mklangkamp/BeachbotsMatt/Basebot Stand/ZEDCamera.SLDPRT

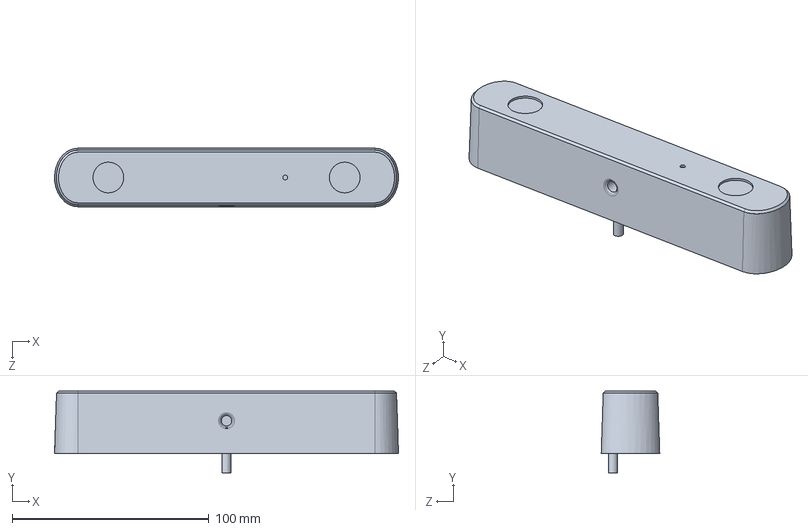
[picture p15: CAD file, 2021-02-08]
Basebot Stand/ZEDCamera.SLDPRT
174.7 x 41.6 x 29.7 mm
