mklangkamp/BeachbotsMatt/Basebot/Steering Motor Mount (Bottom).SLDPRT

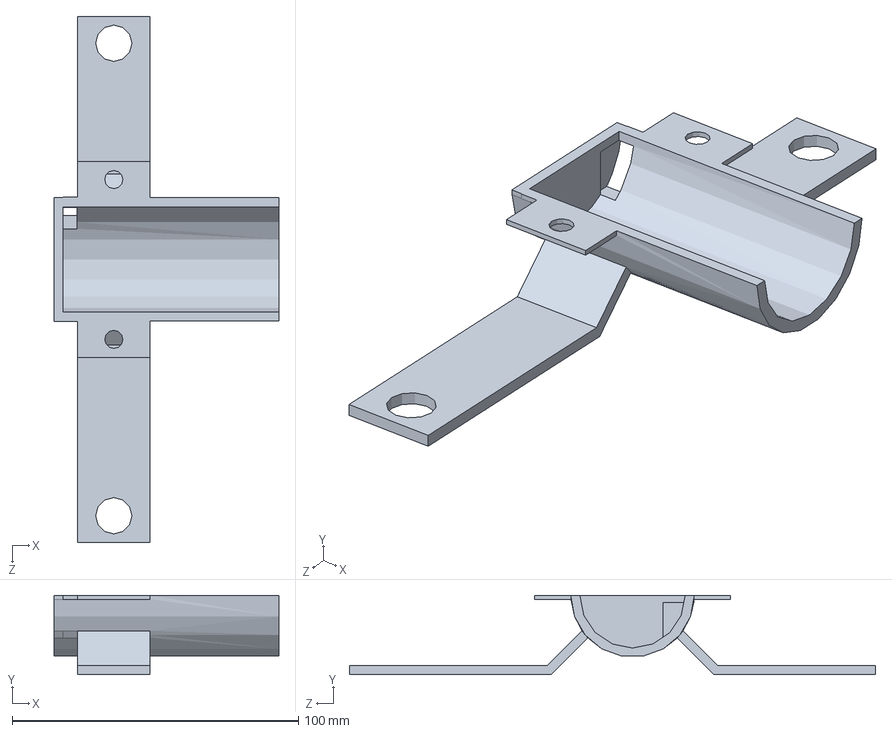
[picture p16: CAD file, 2021-05-04]
Basebot/Steering Motor Mount (Bottom).SLDPRT
78.6 x 27.7 x 183.8 mm
