mklangkamp/BeachbotsMatt/Chassis/CAM (Esprit)/SuspensionPlateAfter1.STL

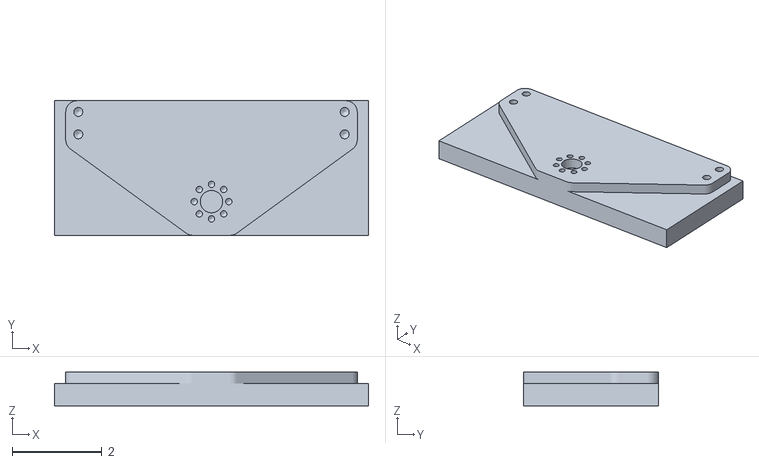
[picture p17: CAD file, 2020-11-09]
Chassis/CAM (Esprit)/SuspensionPlateAfter1.STL
7.00 x 3.00 x 0.75
