mklangkamp/BeachbotsMatt/Chassis/Electronics mount/raspberry pi 4b mount.SLDPRT

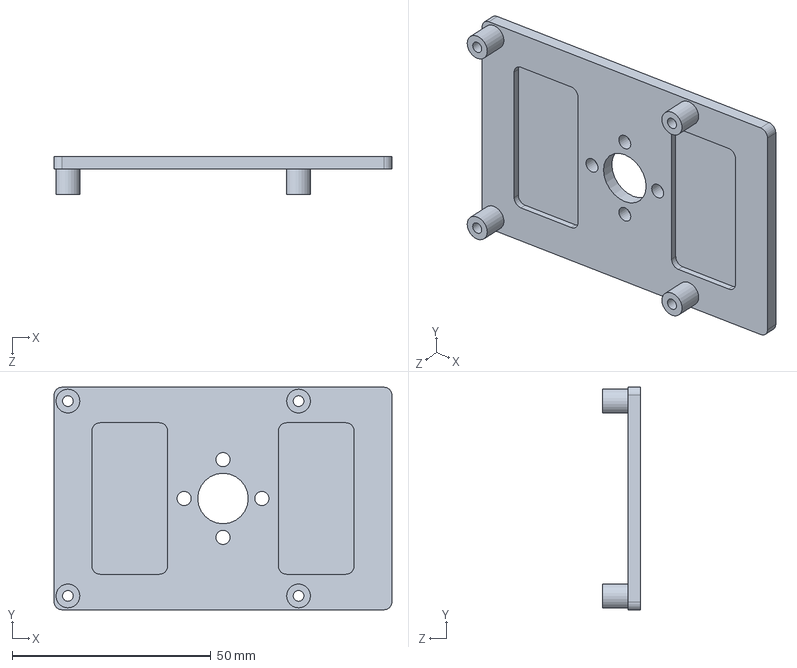
[picture p18: CAD file, 2020-11-25]
Chassis/Electronics mount/raspberry pi 4b mount.SLDPRT
85.0 x 56.0 x 9.53 mm
