mklangkamp/BeachbotsMatt/Chassis/GripperAssemblySlot/ServoHornWithSlotAttachment.SLDPRT

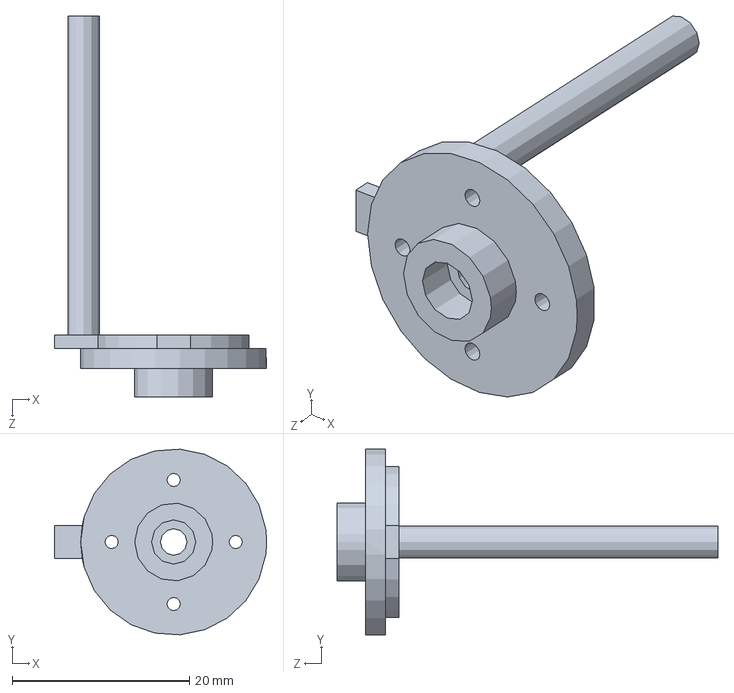
[picture p19: CAD file, 2021-05-04]
Chassis/GripperAssemblySlot/ServoHornWithSlotAttachment.SLDPRT
24.0 x 21.0 x 43.0 mm
