mklangkamp/BeachbotsMatt/Chassis/GrippperAssemblyNEW/Involute Spur Gear Generator - Better 0 3-13 WIDER.SLDPRT

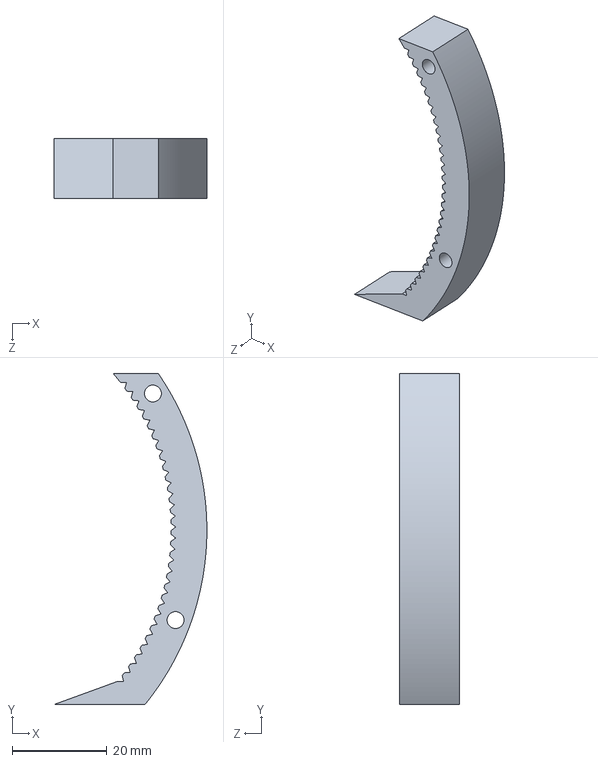
[picture p20: CAD file, 2021-03-24]
Chassis/GrippperAssemblyNEW/Involute Spur Gear Generator - Better 0 3-13 WIDER.SLDPRT
32.2 x 69.8 x 12.7 mm
