mklangkamp/BeachbotsMatt/Chassis/LBracketReinforcement.SLDPRT

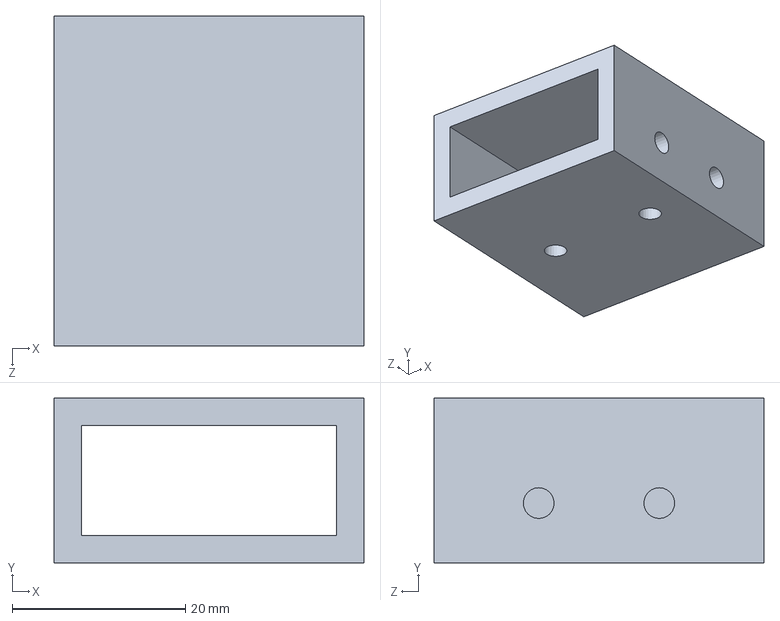
[picture p21: CAD file, 2021-05-04]
Chassis/LBracketReinforcement.SLDPRT
35.8 x 19.1 x 38.1 mm
