mklangkamp/BeachbotsMatt/Basebot Stand/StandOuterShaft.SLDPRT

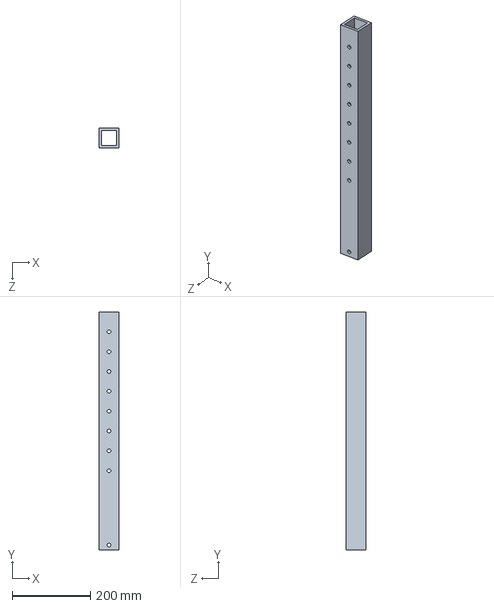
[picture p23: CAD file, 2021-02-08]
Basebot Stand/StandOuterShaft.SLDPRT
50.8 x 609.6 x 50.8 mm
