mklangkamp/BeachbotsMatt/Basebot/Wheel to Axle Adapter.SLDPRT

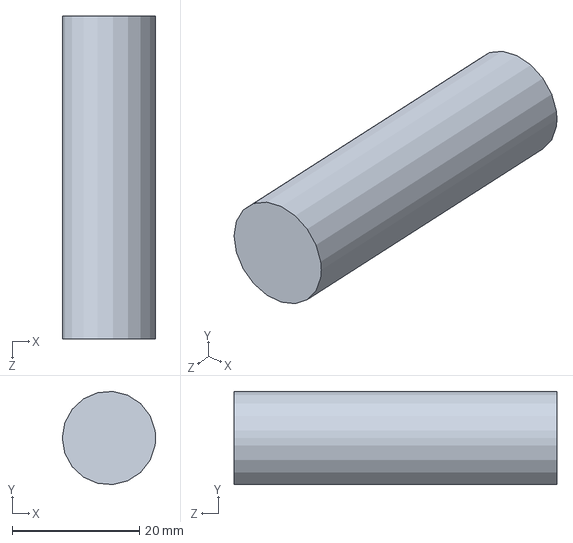
[picture p24: CAD file, 2021-05-04]
Basebot/Wheel to Axle Adapter.SLDPRT
14.7 x 14.6 x 50.8 mm
