mklangkamp/BeachbotsMatt/Chassis/CAM (Esprit)/pillowblockafter2.1.STL

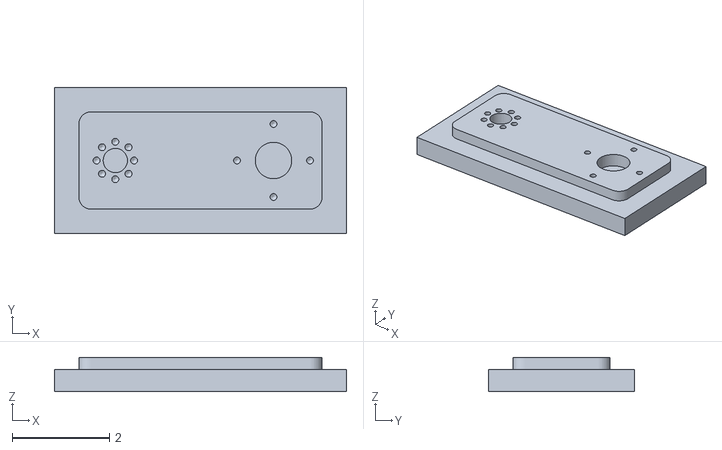
[picture p25: CAD file, 2020-11-09]
Chassis/CAM (Esprit)/pillowblockafter2.1.STL
6.00 x 3.00 x 0.7
