mklangkamp/BeachbotsMatt/Chassis/Electronics mount/stepper motor driver mount.SLDPRT

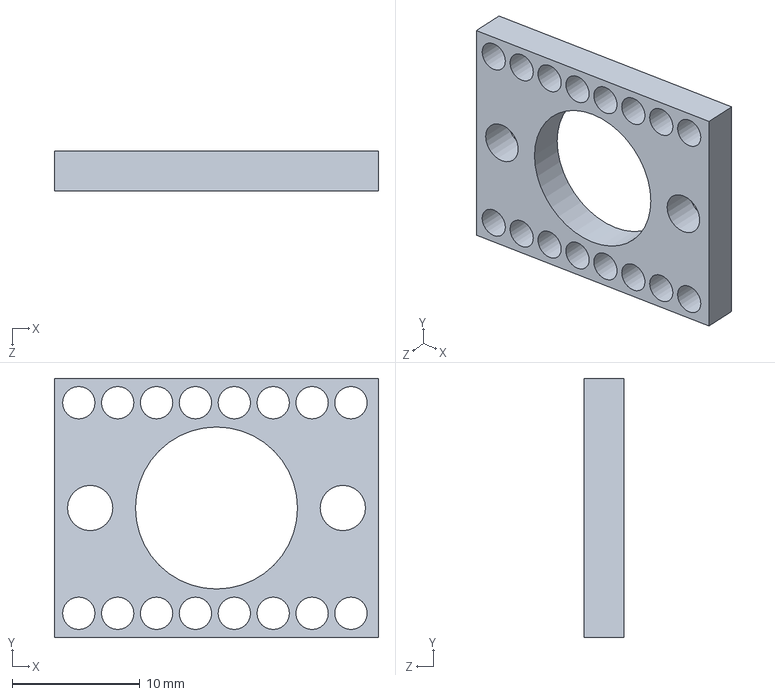
[picture p26: CAD file, 2020-11-23]
Chassis/Electronics mount/stepper motor driver mount.SLDPRT
25.4 x 20.3 x 3.17 mm
