mklangkamp/BeachbotsMatt/Chassis/GripperAssemblySlot/GripperTopBracketNew.SLDPRT

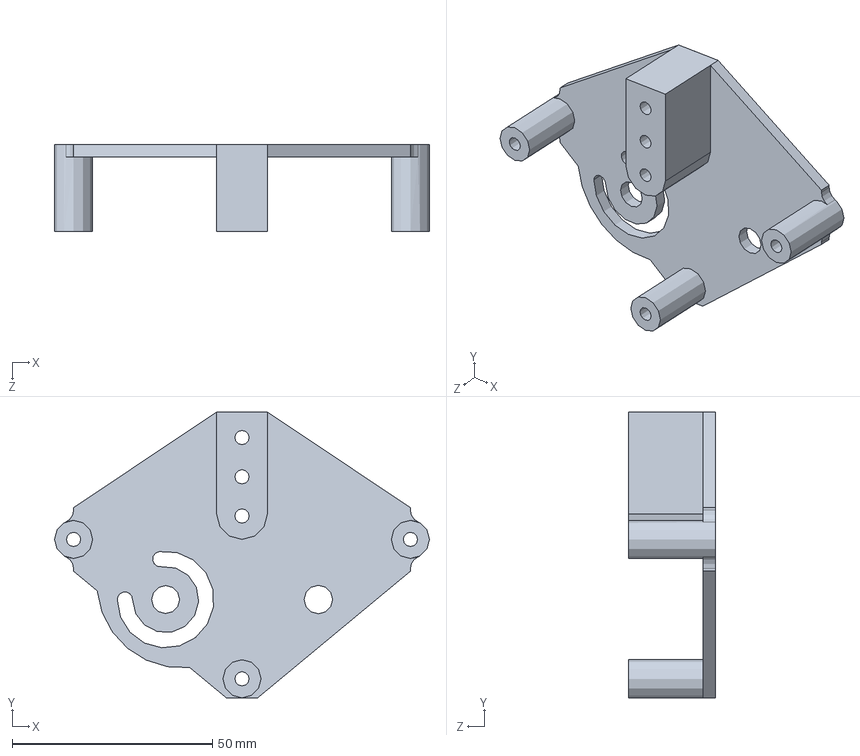
[picture p27: CAD file, 2021-05-04]
Chassis/GripperAssemblySlot/GripperTopBracketNew.SLDPRT
93.5 x 71.3 x 21.7 mm
