mklangkamp/BeachbotsMatt/Chassis/GrippperAssemblyNEW/Involute Spur Gear Generator - Better 0 3-13 EXTRA.SLDPRT

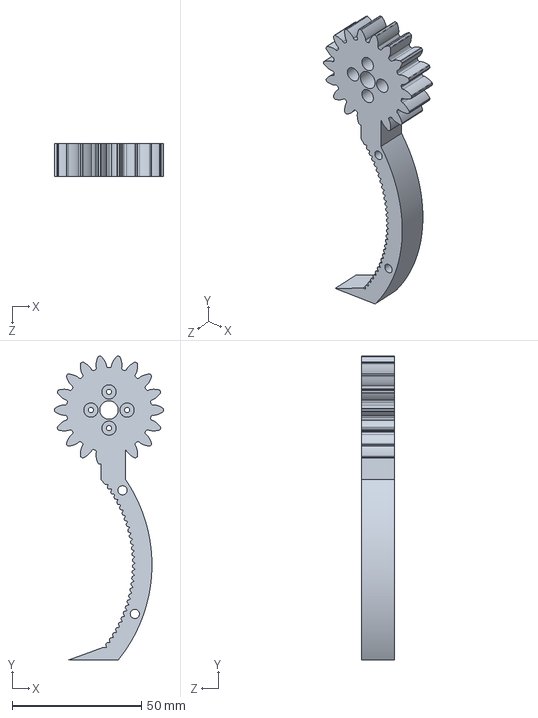
[picture p28: CAD file, 2021-03-24]
Chassis/GrippperAssemblyNEW/Involute Spur Gear Generator - Better 0 3-13 EXTRA.SLDPRT
42.3 x 117.6 x 12.7 mm
