mklangkamp/BeachbotsMatt/Chassis/New Gripper Designs/GripperArmBracket.SLDPRT

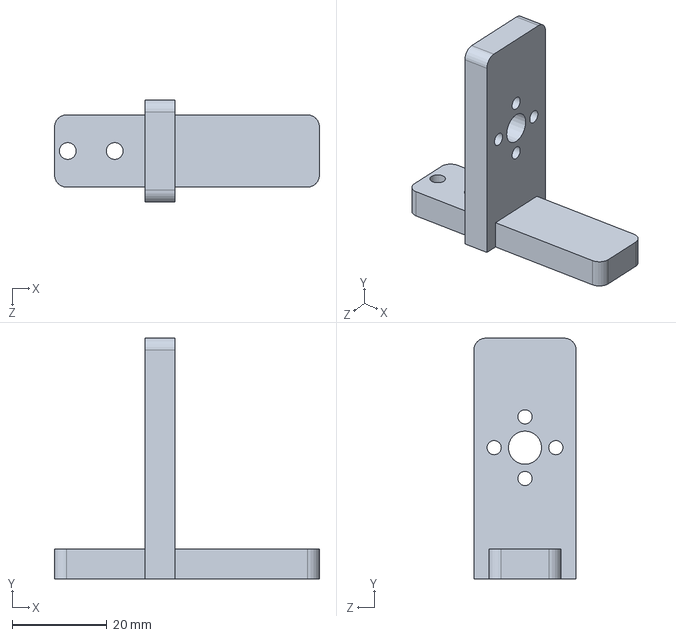
[picture p29: CAD file, 2020-12-01]
Chassis/New Gripper Designs/GripperArmBracket.SLDPRT
55.9 x 50.8 x 21.6 mm
