mklangkamp/BeachbotsMatt/Chassis/New Gripper Designs/GripperRedesignOne/GearBase.SLDPRT

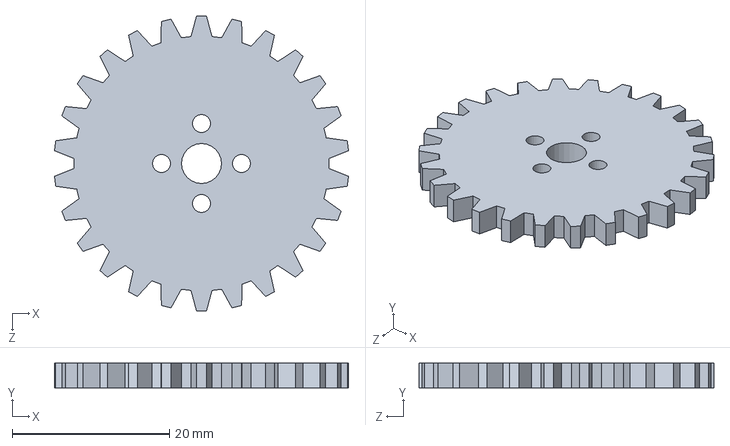
[picture p30: CAD file, 2021-03-08]
Chassis/New Gripper Designs/GripperRedesignOne/GearBase.SLDPRT
37.4 x 3.17 x 37.5 mm
