mklangkamp/BeachbotsMatt/Chassis/power swtich mount.SLDPRT

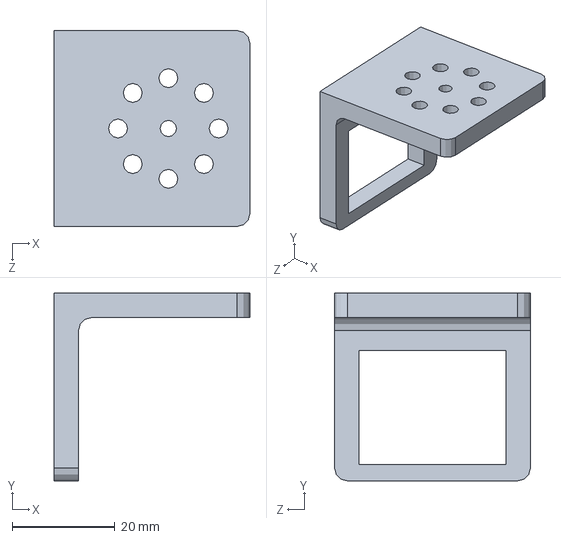
[picture p31: CAD file, 2021-03-30]
Chassis/power swtich mount.SLDPRT
38.1 x 36.5 x 38.1 mm
