mklangkamp/BeachbotsMatt/Chassis/Electronics mount/servo controller mount.SLDPRT

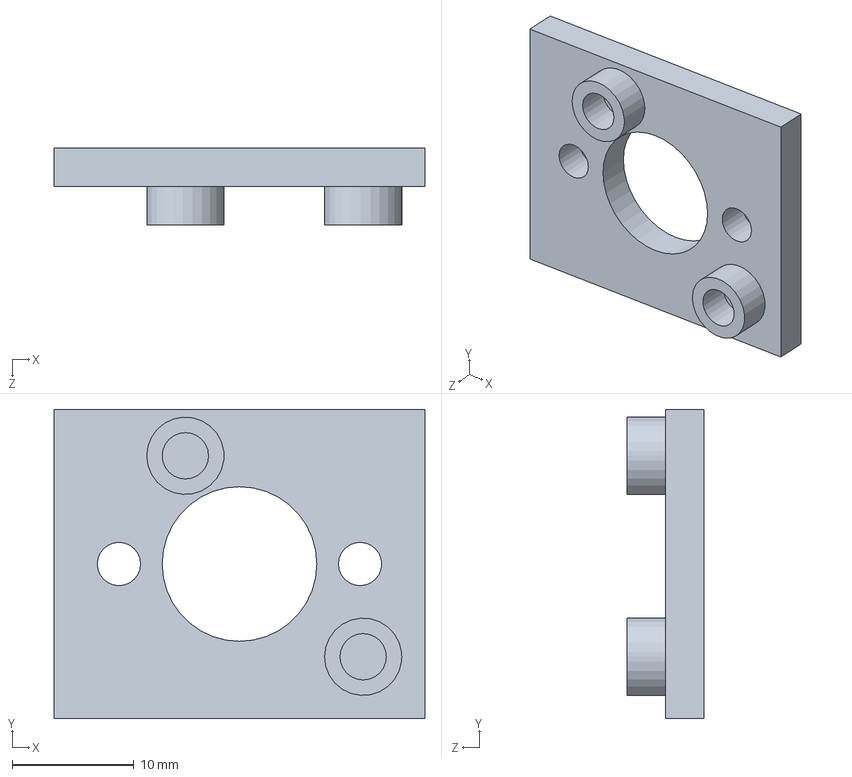
[picture p32: CAD file, 2020-11-23]
Chassis/Electronics mount/servo controller mount.SLDPRT
30.5 x 25.4 x 6.35 mm
