mklangkamp/BeachbotsMatt/Chassis/New Gripper Designs/Gripper_Connector.SLDPRT

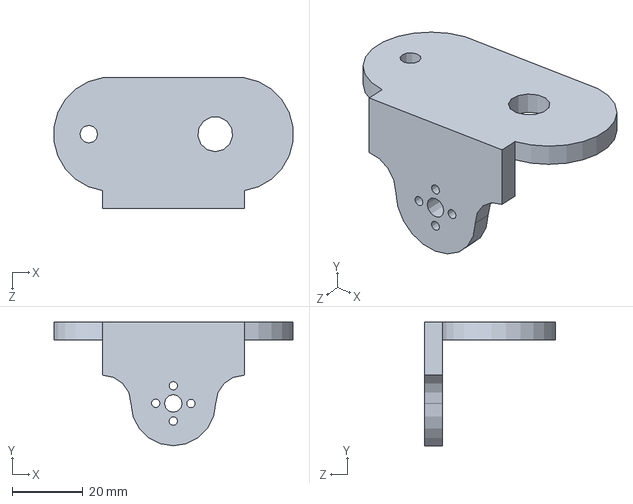
[picture p33: CAD file, 2020-11-23]
Chassis/New Gripper Designs/Gripper_Connector.SLDPRT
67.7 x 35.0 x 37.0 mm
