mklangkamp/BeachbotsMatt/Chassis/NewShoulderReinforcementLink.SLDPRT

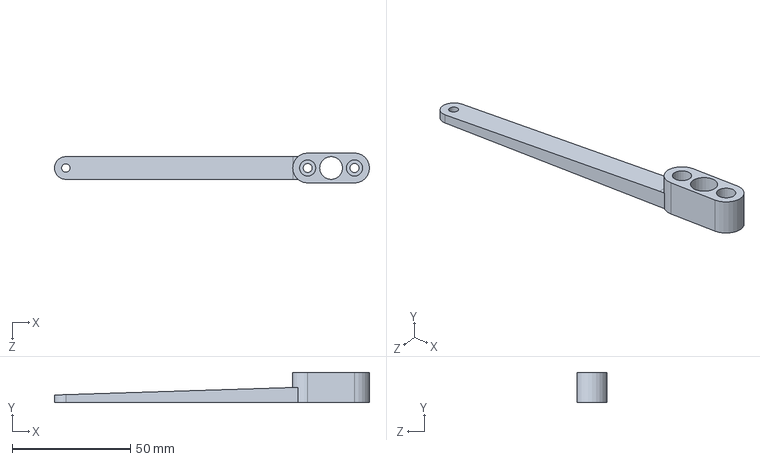
[picture p34: CAD file, 2021-03-08]
Chassis/NewShoulderReinforcementLink.SLDPRT
133.3 x 12.7 x 12.7 mm
