mklangkamp/BeachbotsMatt/Basebot Stand/38inPin.SLDPRT

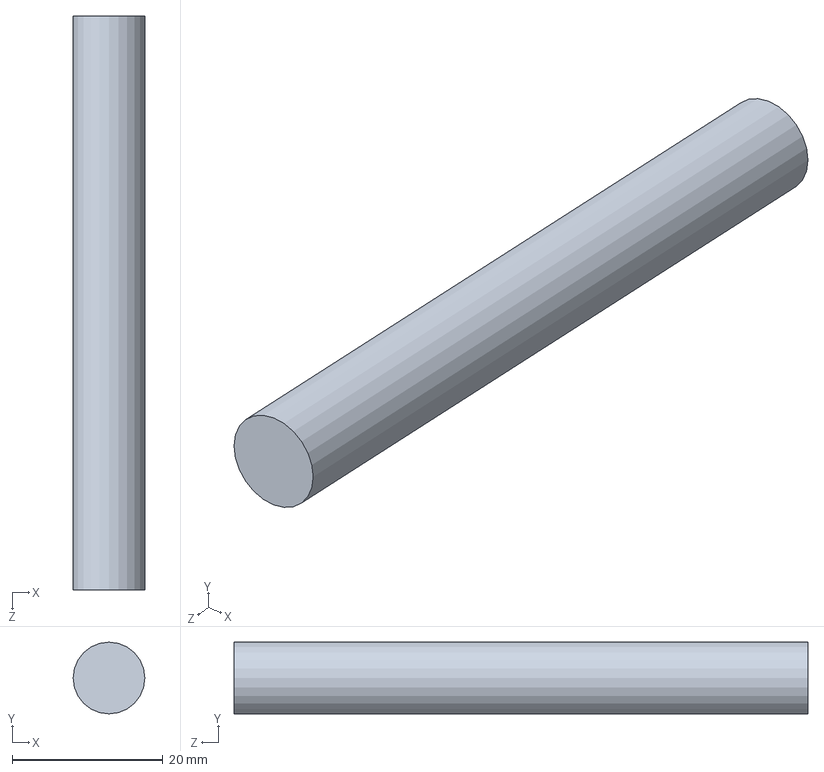
[picture p35: CAD file, 2021-02-08]
Basebot Stand/38inPin.SLDPRT
9.53 x 9.53 x 76.2 mm
