mklangkamp/BeachbotsMatt/Basebot/Wheel.SLDPRT

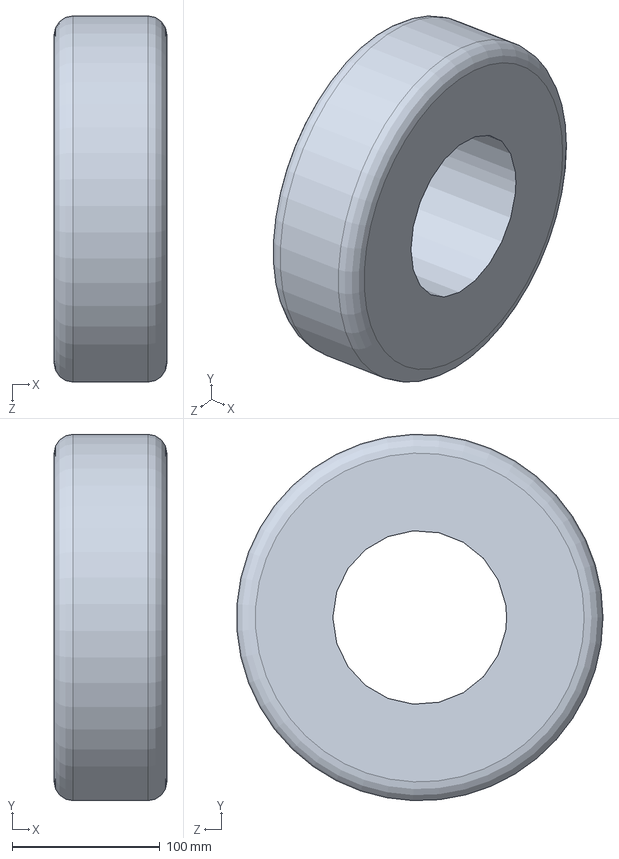
[picture p36: CAD file, 2021-05-04]
Basebot/Wheel.SLDPRT
76.2 x 247.5 x 247.3 mm
