mklangkamp/BeachbotsMatt/Chassis/GripperAssemblySlot/Connector Bracket.SLDPRT

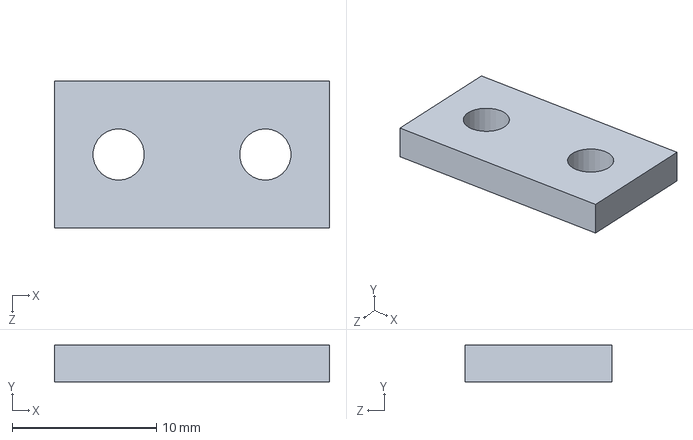
[picture p37: CAD file, 2021-05-04]
Chassis/GripperAssemblySlot/Connector Bracket.SLDPRT
19.1 x 2.54 x 10.2 mm
