mklangkamp/BeachbotsMatt/Chassis/GrippperAssemblyNEW/GripperRedesign.SLDPRT

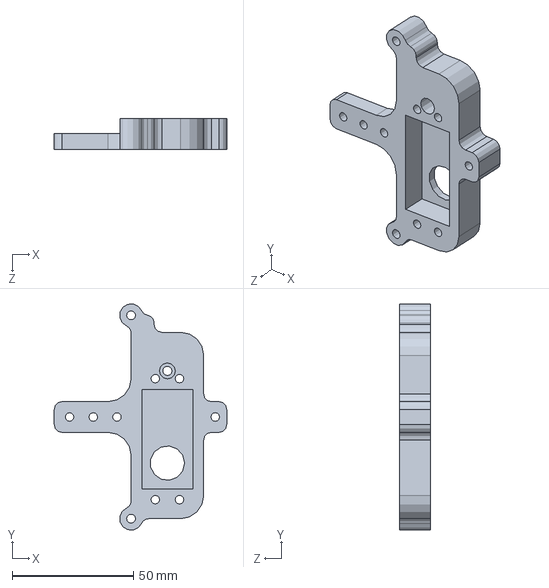
[picture p38: CAD file, 2021-03-19]
Chassis/GrippperAssemblyNEW/GripperRedesign.SLDPRT
71.3 x 93.4 x 13.0 mm
