mklangkamp/BeachbotsMatt/Chassis/New Gripper Designs/Gripper_Finger.SLDPRT

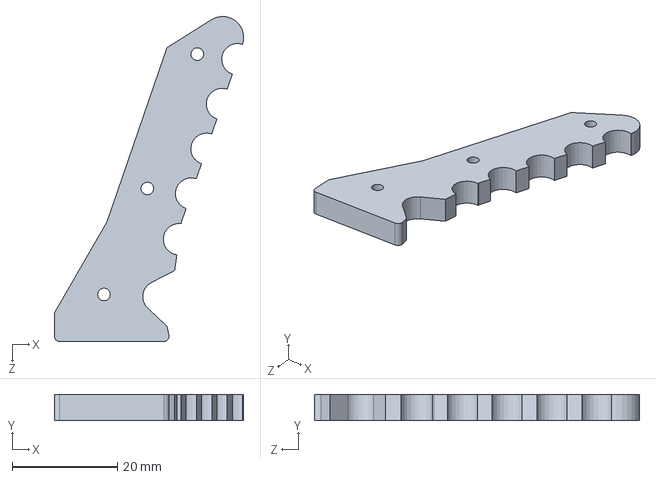
[picture p39: CAD file, 2020-11-23]
Chassis/New Gripper Designs/Gripper_Finger.SLDPRT
36.0 x 5.00 x 61.8 mm
