mklangkamp/BeachbotsMatt/Chassis/New Gripper Designs/GripperRedesignOne/NewGear.SLDPRT

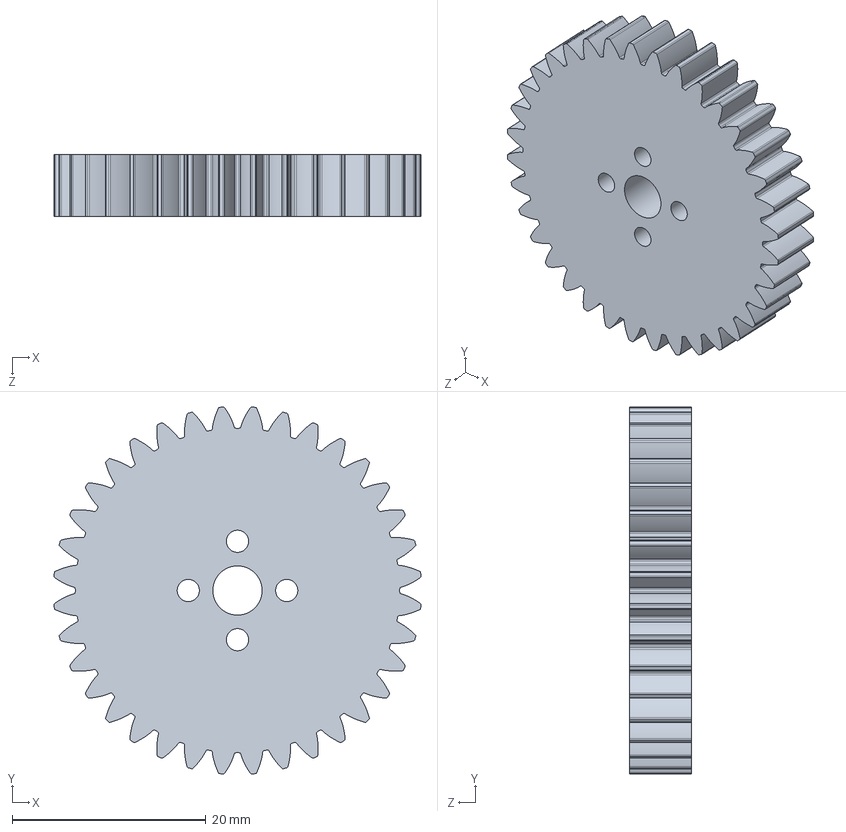
[picture p40: CAD file, 2021-03-08]
Chassis/New Gripper Designs/GripperRedesignOne/NewGear.SLDPRT
37.9 x 37.9 x 6.35 mm
