mklangkamp/BeachbotsMatt/Chassis/ShoulderLinkReinforcement.SLDPRT

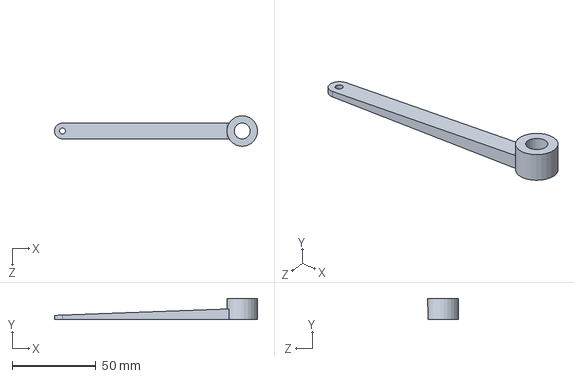
[picture p41: CAD file, 2021-03-08]
Chassis/ShoulderLinkReinforcement.SLDPRT
121.3 x 12.7 x 18.3 mm
