mklangkamp/BeachbotsMatt/Basebot Stand/StandBottomCartConnector.SLDPRT

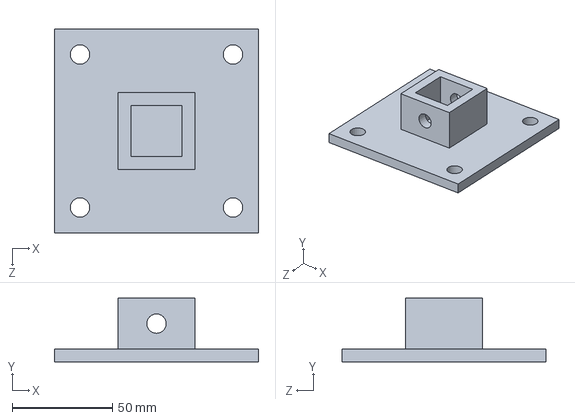
[picture p42: CAD file, 2021-02-08]
Basebot Stand/StandBottomCartConnector.SLDPRT
101.6 x 31.8 x 101.6 mm
