mklangkamp/BeachbotsMatt/Basebot/Steering Motor Mount (Top).SLDPRT

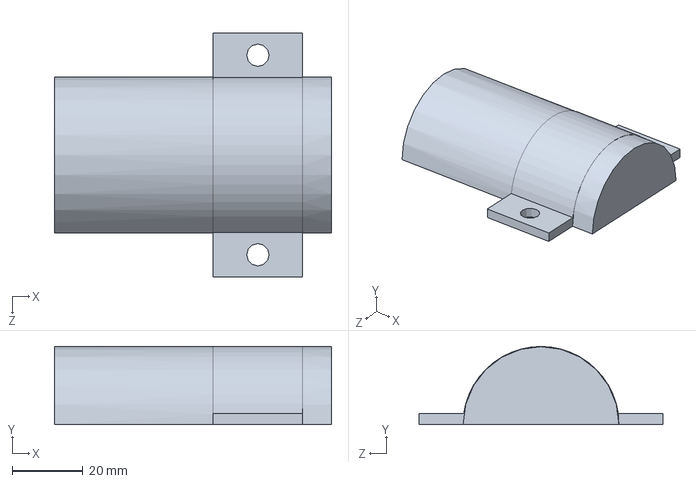
[picture p43: CAD file, 2021-05-04]
Basebot/Steering Motor Mount (Top).SLDPRT
78.6 x 22.2 x 69.3 mm
