mklangkamp/BeachbotsMatt/Chassis/Apriltag mount.SLDPRT

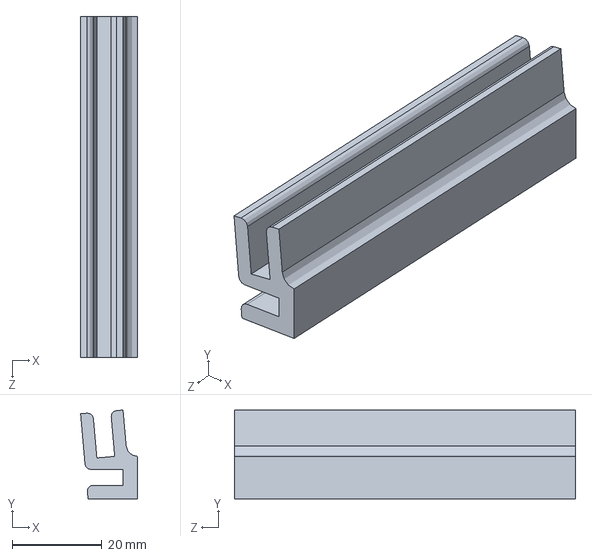
[picture p44: CAD file, 2021-02-22]
Chassis/Apriltag mount.SLDPRT
12.7 x 19.9 x 76.2 mm
