mklangkamp/BeachbotsMatt/Chassis/GripperAssemblySlot/ServoHolderBracketNew.SLDPRT

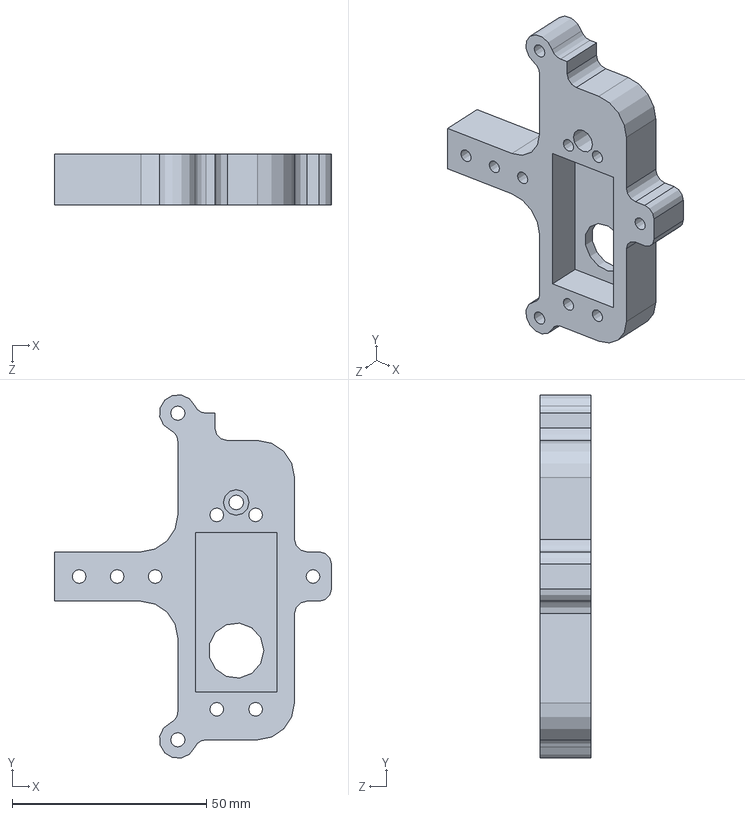
[picture p45: CAD file, 2021-05-04]
Chassis/GripperAssemblySlot/ServoHolderBracketNew.SLDPRT
71.3 x 93.4 x 13.0 mm
