mklangkamp/BeachbotsMatt/Chassis/GrippperAssemblyNEW/bottle.SLDPRT

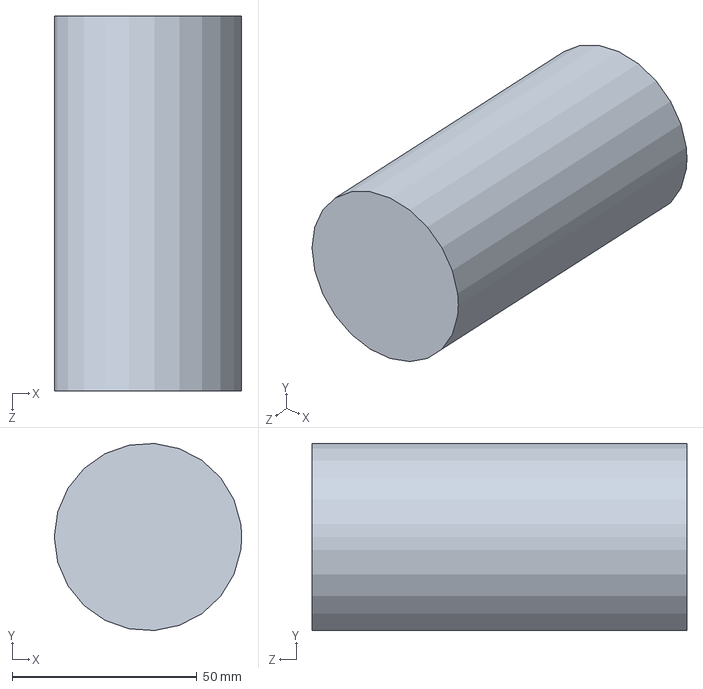
[picture p46: CAD file, 2021-03-19]
Chassis/GrippperAssemblyNEW/bottle.SLDPRT
50.8 x 50.7 x 101.6 mm
