mklangkamp/BeachbotsMatt/Chassis/New Gripper Designs/GripperRedesignOne/SpringLoadArm.SLDPRT

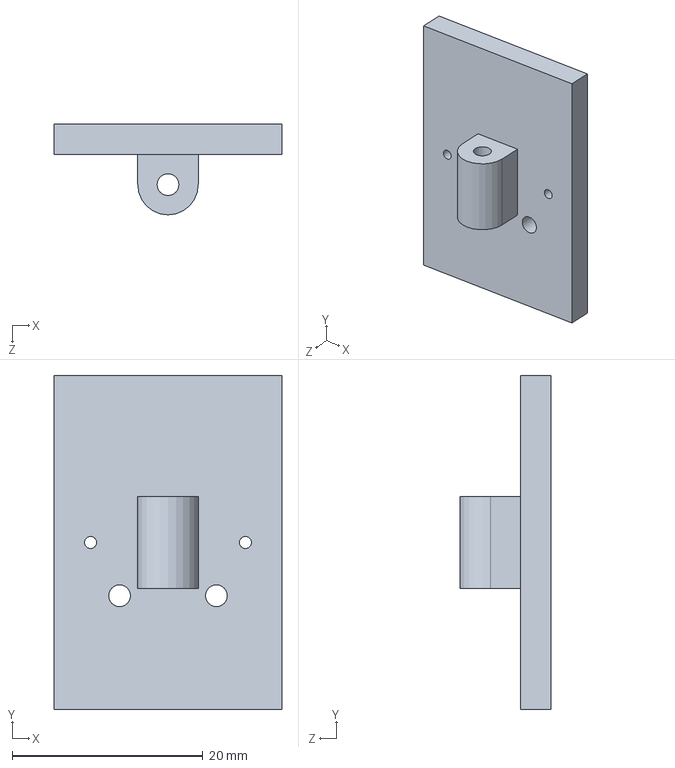
[picture p47: CAD file, 2021-03-08]
Chassis/New Gripper Designs/GripperRedesignOne/SpringLoadArm.SLDPRT
23.9 x 35.1 x 9.53 mm
