mklangkamp/BeachbotsMatt/Chassis/New Gripper Designs/SiftPlate.SLDPRT

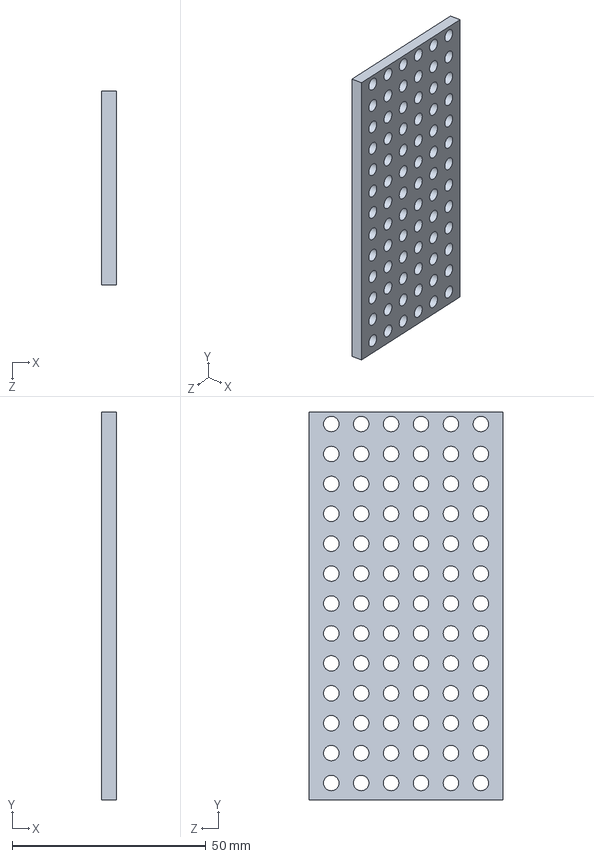
[picture p48: CAD file, 2020-11-23]
Chassis/New Gripper Designs/SiftPlate.SLDPRT
3.75 x 100.0 x 50.0 mm
