mklangkamp/BeachbotsMatt/Basebot Stand/StandInnerShaft.SLDPRT

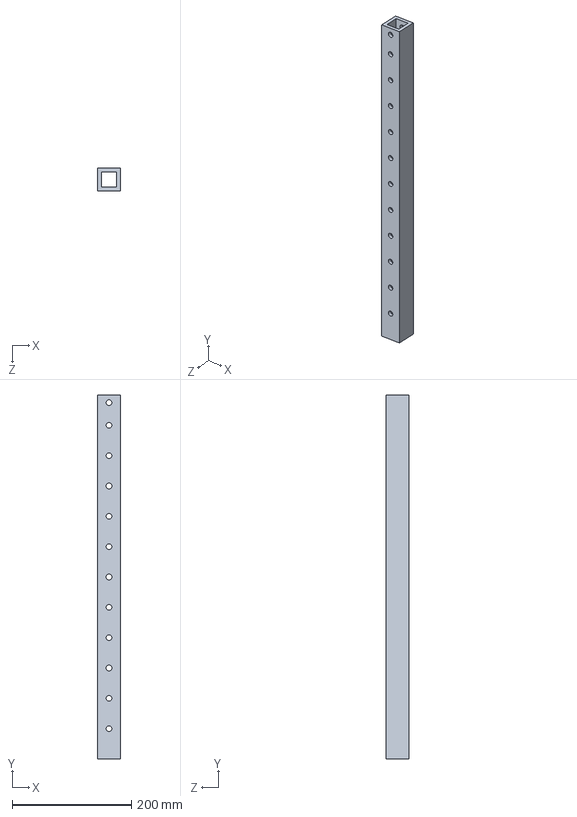
[picture p49: CAD file, 2021-02-08]
Basebot Stand/StandInnerShaft.SLDPRT
38.1 x 609.6 x 38.1 mm
