mklangkamp/BeachbotsMatt/Basebot/R155-2RS Mini ball Bearing.SLDPRT

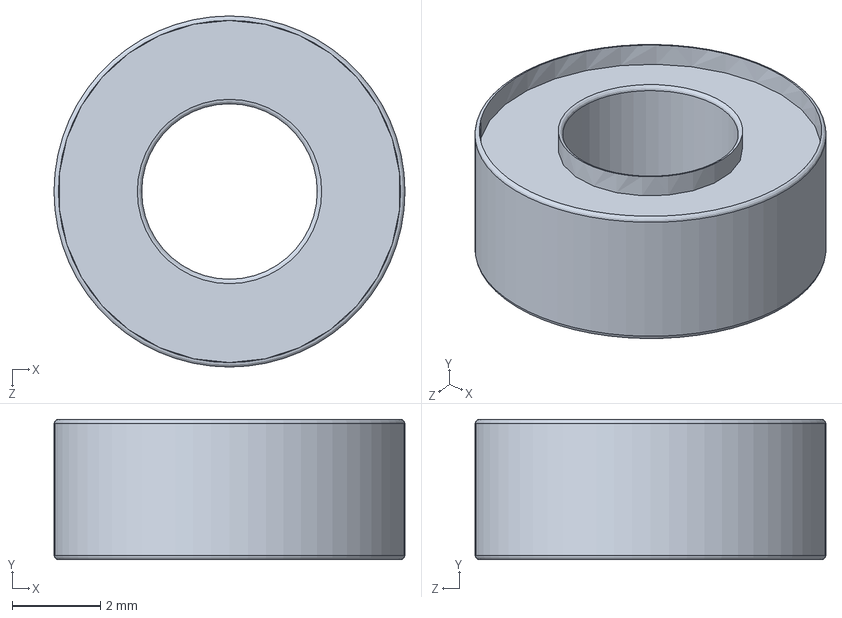
[picture p50: CAD file, 2021-05-04]
Basebot/R155-2RS Mini ball Bearing.SLDPRT
7.94 x 3.17 x 7.94 mm
