mklangkamp/BeachbotsMatt/Chassis/GripperAssemblySlot/MiddlePlate.SLDPRT

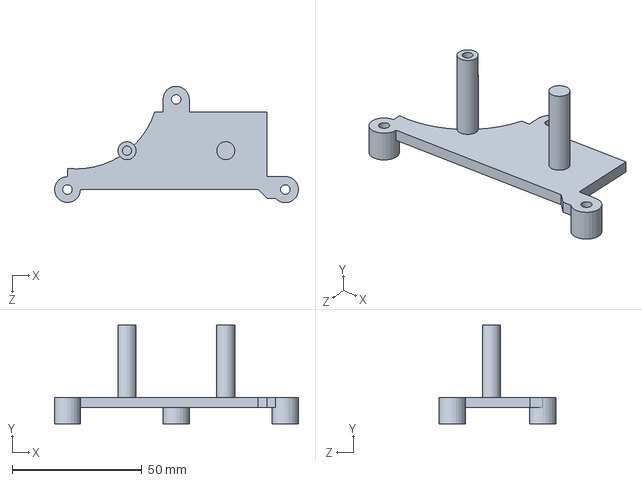
[picture p51: CAD file, 2021-05-04]
Chassis/GripperAssemblySlot/MiddlePlate.SLDPRT
94.1 x 38.1 x 44.9 mm
