mklangkamp/BeachbotsMatt/Chassis/GrippperAssemblyNEW/GripperRedesign2.SLDPRT

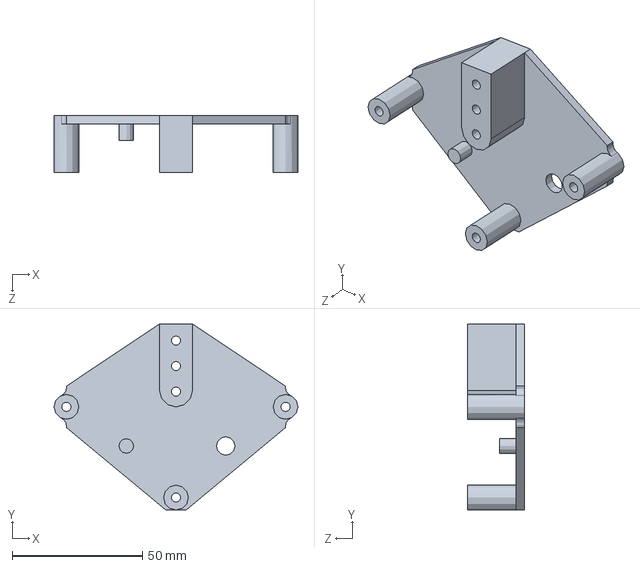
[picture p52: CAD file, 2021-03-19]
Chassis/GrippperAssemblyNEW/GripperRedesign2.SLDPRT
93.5 x 71.3 x 21.7 mm
