mklangkamp/BeachbotsMatt/Chassis/MotorCoverBracketOne.SLDPRT

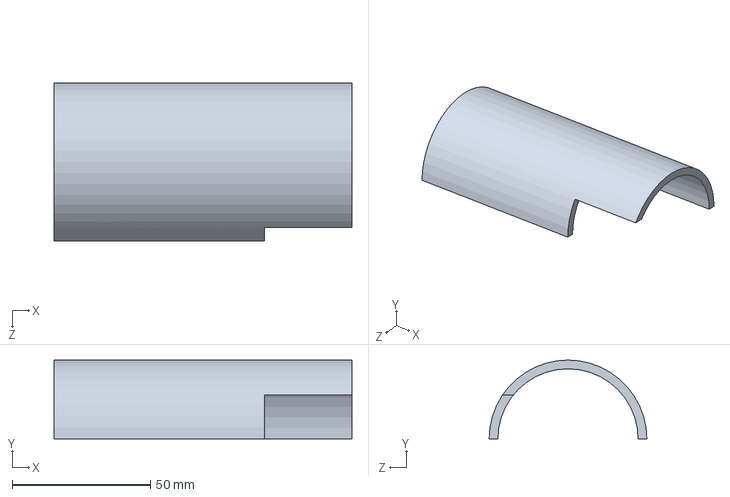
[picture p53: CAD file, 2021-02-22]
Chassis/MotorCoverBracketOne.SLDPRT
108.0 x 28.6 x 57.1 mm
