mklangkamp/BeachbotsMatt/Chassis/New Gripper Designs/Gripper_Finger_Driven.SLDPRT

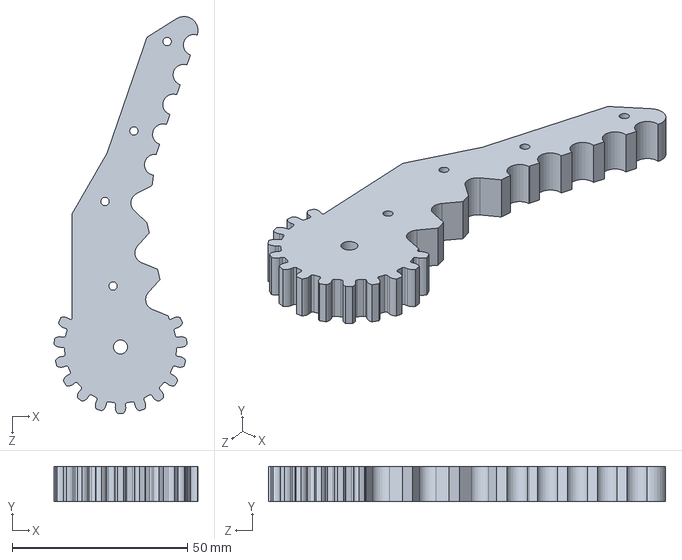
[picture p54: CAD file, 2020-11-23]
Chassis/New Gripper Designs/Gripper_Finger_Driven.SLDPRT
41.1 x 10.0 x 113.3 mm
