mklangkamp/BeachbotsMatt/Chassis/New Gripper Designs/GripperRedesignOne/ServoHorn.SLDPRT

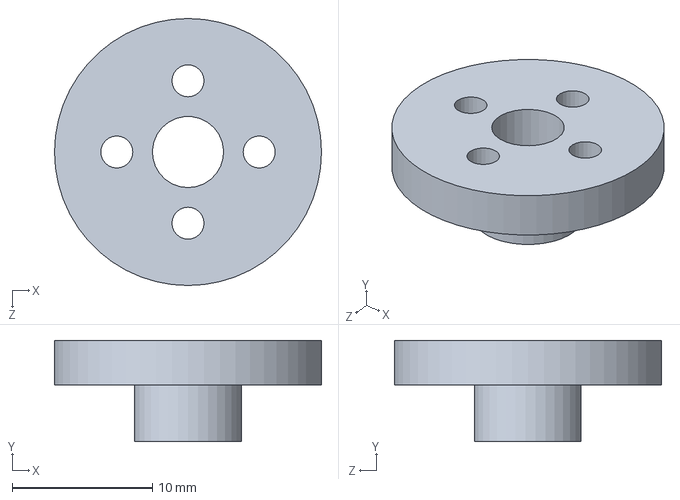
[picture p55: CAD file, 2021-03-08]
Chassis/New Gripper Designs/GripperRedesignOne/ServoHorn.SLDPRT
19.1 x 7.24 x 19.1 mm
