mklangkamp/BeachbotsMatt/Basebot/Rack.SLDPRT

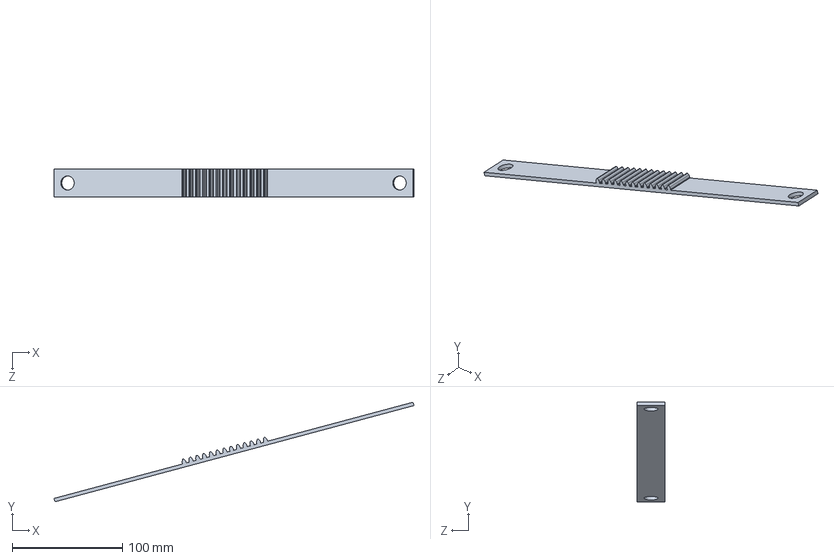
[picture p56: CAD file, 2021-05-04]
Basebot/Rack.SLDPRT
326.2 x 90.3 x 25.4 mm
