mklangkamp/BeachbotsMatt/Chassis/GrippperAssemblyNEW/horn.SLDPRT

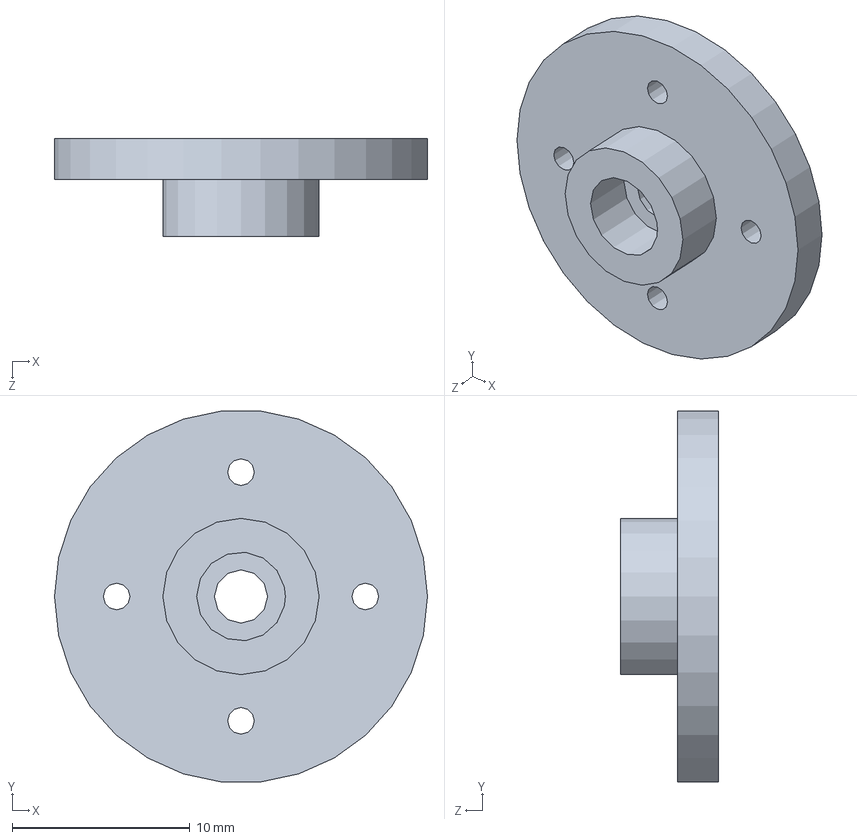
[picture p57: CAD file, 2021-03-19]
Chassis/GrippperAssemblyNEW/horn.SLDPRT
21.0 x 20.9 x 5.50 mm
