mklangkamp/BeachbotsMatt/Chassis/New Gripper Designs/Finger_Extension.SLDPRT

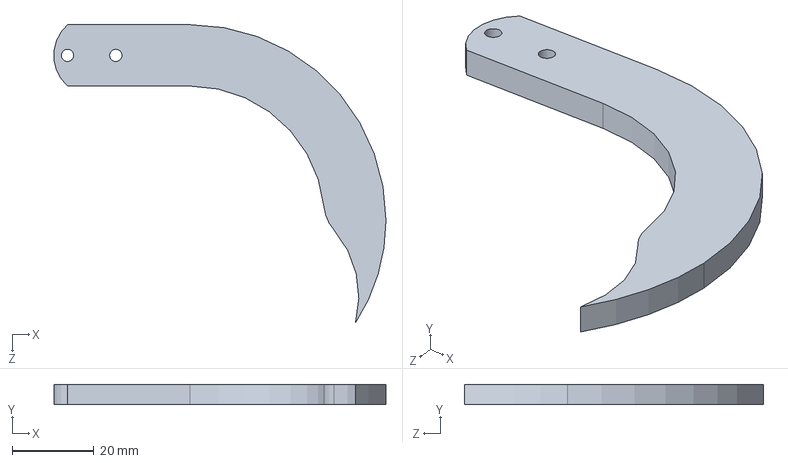
[picture p58: CAD file, 2020-11-23]
Chassis/New Gripper Designs/Finger_Extension.SLDPRT
81.2 x 5.00 x 73.0 mm
