mklangkamp/BeachbotsMatt/Basebot Stand/StandBottomCartBracket.SLDPRT

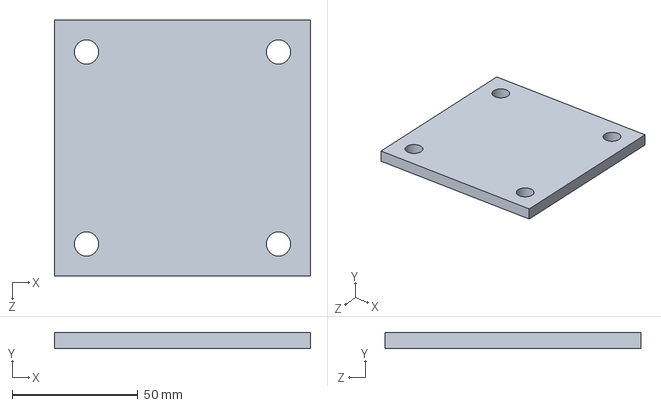
[picture p59: CAD file, 2021-02-08]
Basebot Stand/StandBottomCartBracket.SLDPRT
101.6 x 6.35 x 101.6 mm
