mklangkamp/BeachbotsMatt/Basebot/Pivot Arm (Right).SLDPRT

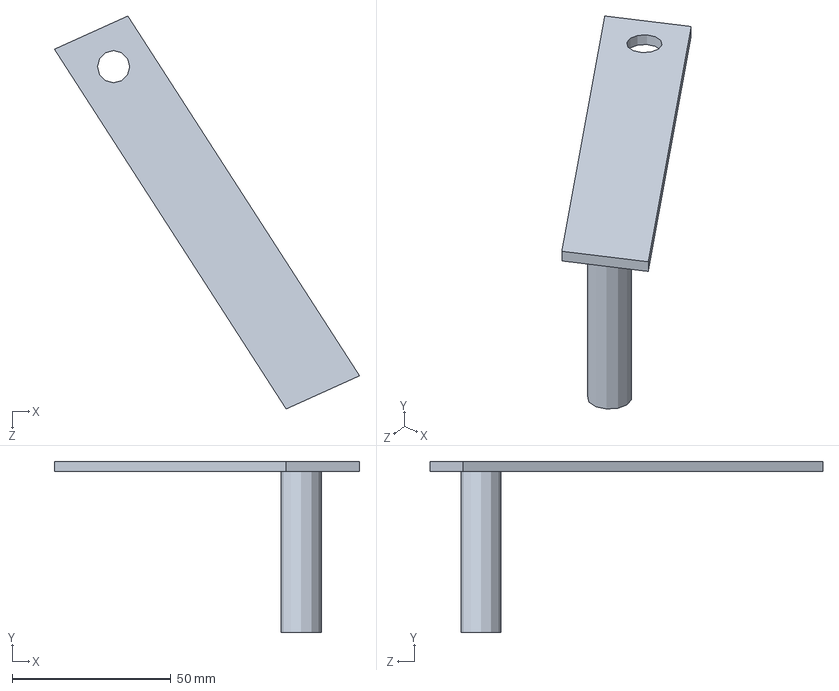
[picture p60: CAD file, 2021-05-04]
Basebot/Pivot Arm (Right).SLDPRT
96.2 x 54.0 x 123.8 mm
