mklangkamp/BeachbotsMatt/Chassis/AprilTag Clip.SLDPRT

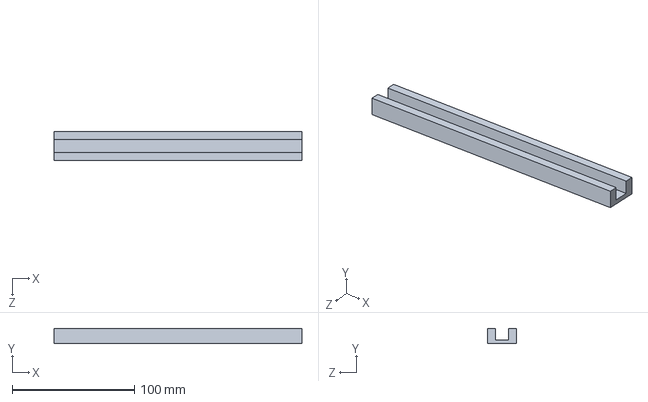
[picture p61: CAD file, 2021-02-22]
Chassis/AprilTag Clip.SLDPRT
203.2 x 12.7 x 23.6 mm
