mklangkamp/BeachbotsMatt/Chassis/GripperAssemblySlot/RubberBandStandOff.SLDPRT

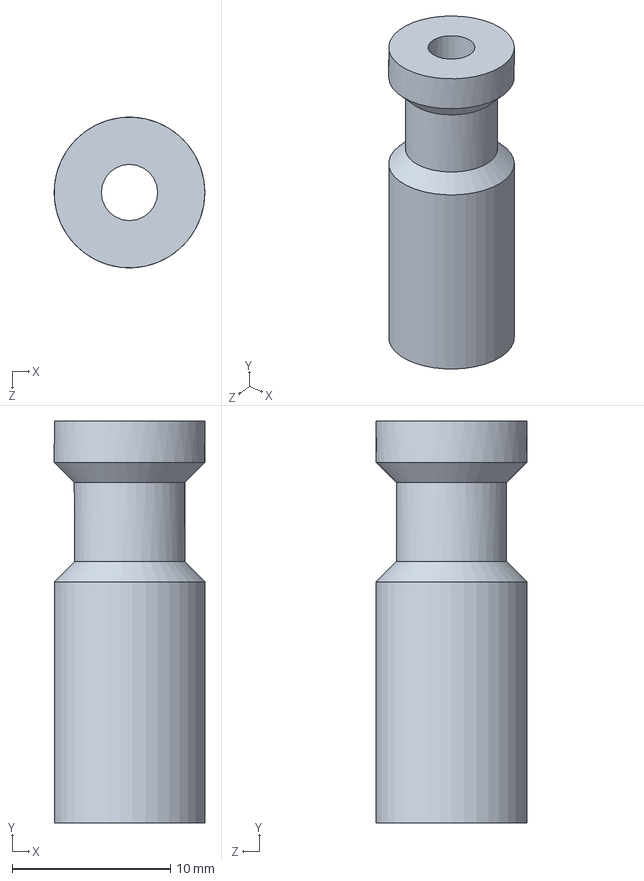
[picture p62: CAD file, 2021-05-04]
Chassis/GripperAssemblySlot/RubberBandStandOff.SLDPRT
9.53 x 25.4 x 9.52 mm
