mklangkamp/BeachbotsMatt/Chassis/New Gripper Designs/Gripper_Finger_Driver.SLDPRT

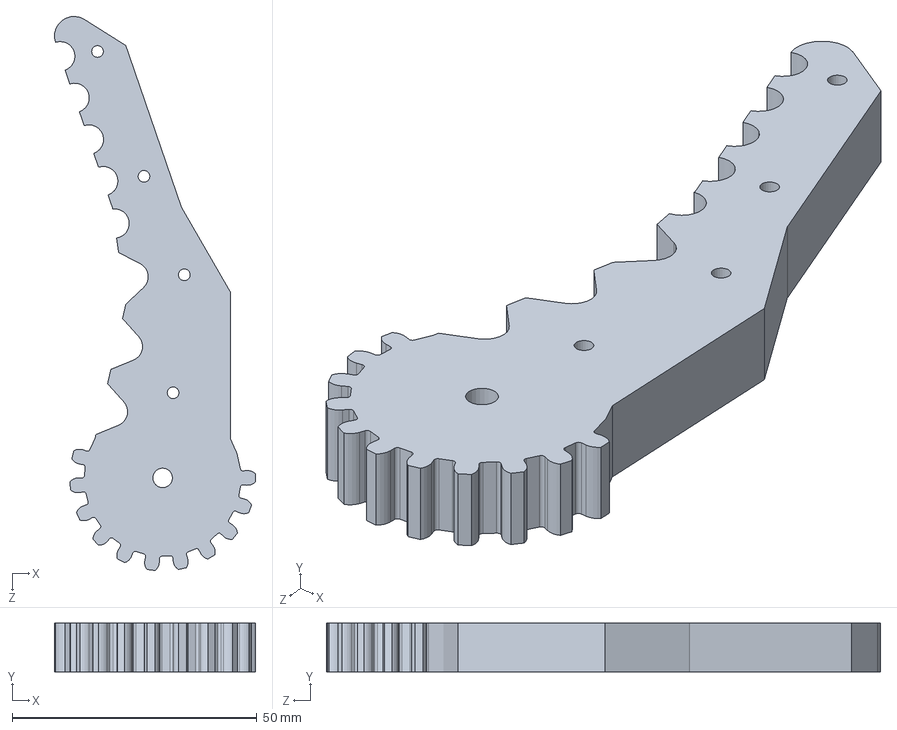
[picture p63: CAD file, 2020-11-23]
Chassis/New Gripper Designs/Gripper_Finger_Driver.SLDPRT
41.1 x 10.0 x 113.3 mm
