mklangkamp/BeachbotsMatt/Chassis/New Gripper Designs/GripperRedesignOne/FingerOne.SLDPRT

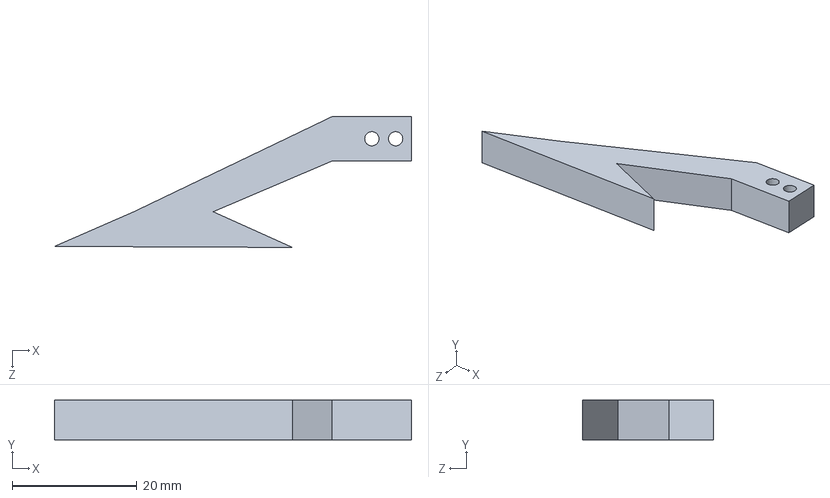
[picture p64: CAD file, 2021-03-08]
Chassis/New Gripper Designs/GripperRedesignOne/FingerOne.SLDPRT
57.1 x 6.35 x 21.0 mm
