mklangkamp/BeachbotsMatt/Basebot/Rear Axle.SLDPRT

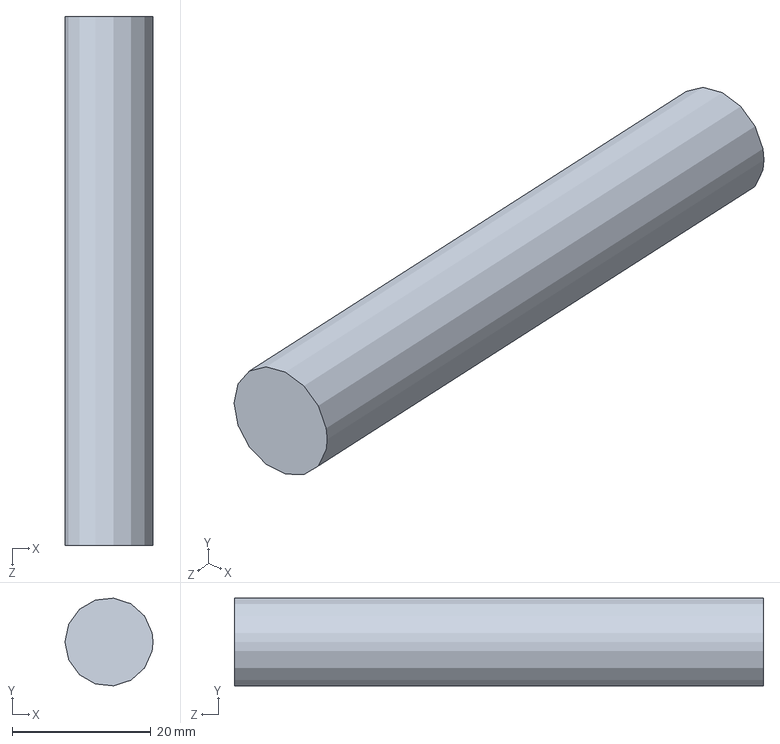
[picture p65: CAD file, 2021-05-04]
Basebot/Rear Axle.SLDPRT
12.7 x 12.6 x 76.2 mm
