mklangkamp/BeachbotsMatt/Chassis/3-8 spacer for imu.SLDPRT

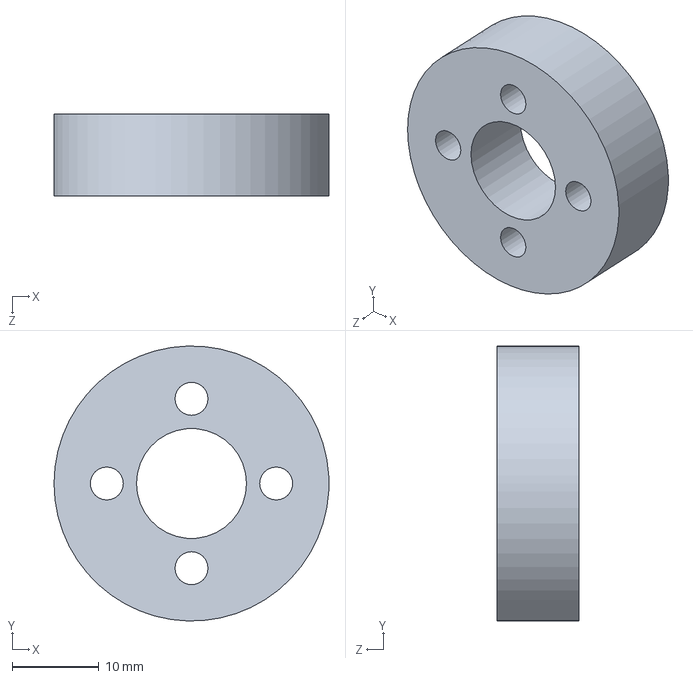
[picture p66: CAD file, 2021-02-03]
Chassis/3-8 spacer for imu.SLDPRT
31.8 x 31.7 x 9.53 mm
