mklangkamp/BeachbotsMatt/Chassis/GripperAssemblySlot/Servo 20kg elbow and gripper2.SLDPRT

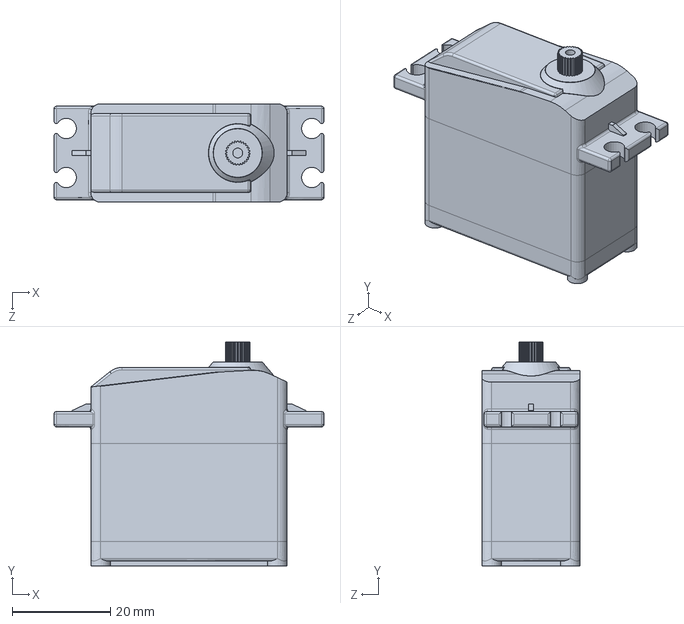
[picture p67: CAD file, 2021-03-19]
Chassis/GripperAssemblySlot/Servo 20kg elbow and gripper2.SLDPRT
55.1 x 45.7 x 20.1 mm
