mklangkamp/BeachbotsMatt/Chassis/New Gripper Designs/GripperRedesignOne/Plate.SLDPRT

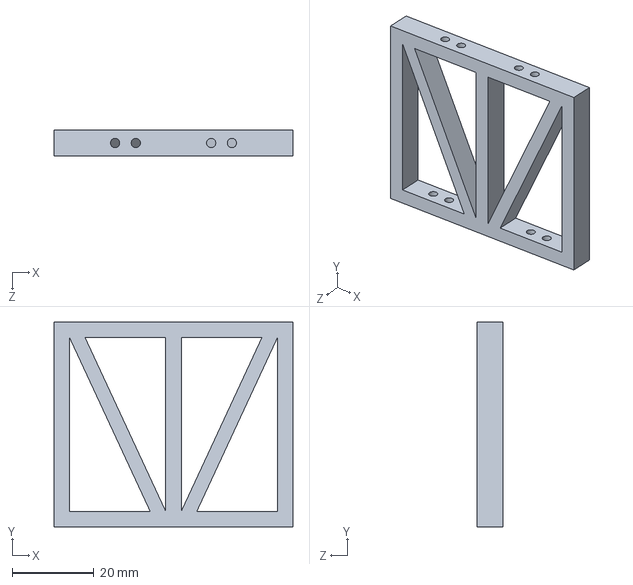
[picture p68: CAD file, 2021-03-08]
Chassis/New Gripper Designs/GripperRedesignOne/Plate.SLDPRT
58.4 x 50.0 x 6.35 mm
