mklangkamp/BeachbotsMatt/Basebot/Radial Ball Bearing 17mm Bore.SLDPRT

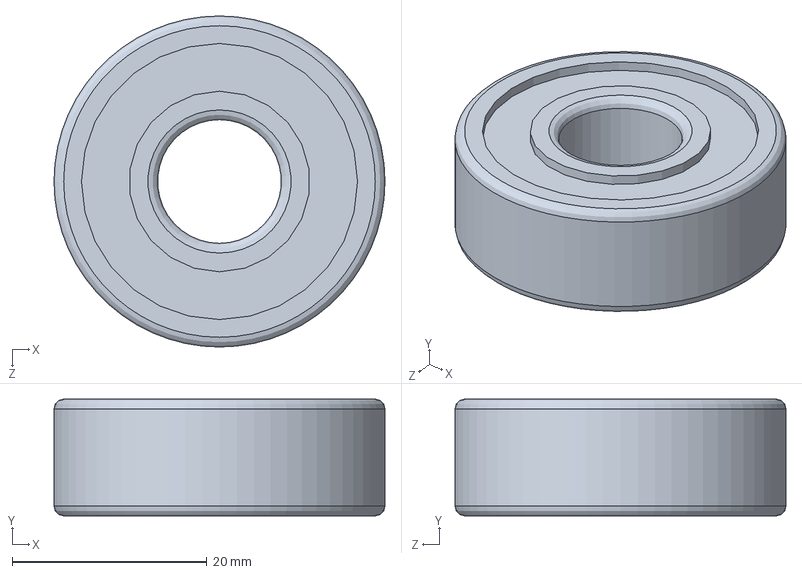
[picture p69: CAD file, 2021-05-04]
Basebot/Radial Ball Bearing 17mm Bore.SLDPRT
34.0 x 12.0 x 34.0 mm
