mklangkamp/BeachbotsMatt/Chassis/Adafruit IMU mount.SLDPRT

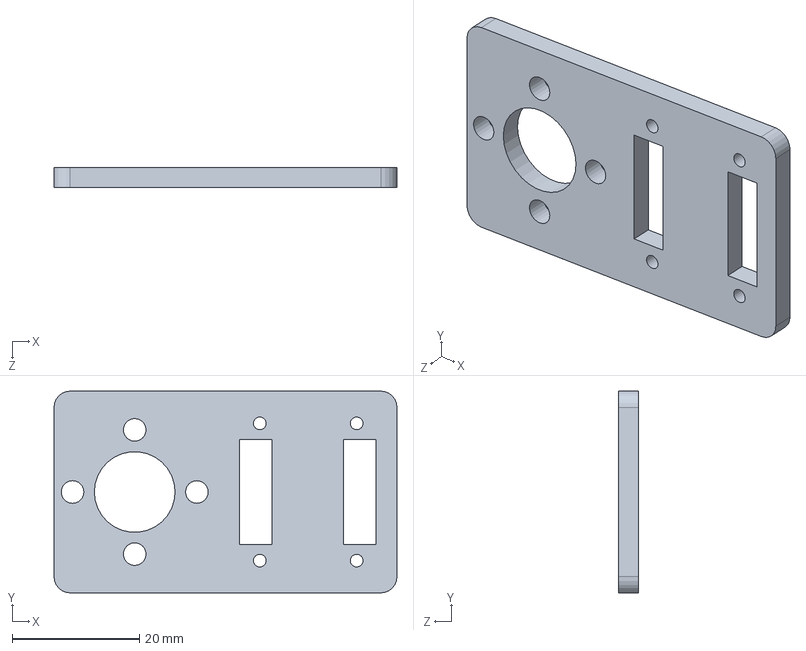
[picture p70: CAD file, 2021-01-31]
Chassis/Adafruit IMU mount.SLDPRT
54.0 x 31.8 x 3.17 mm
