mklangkamp/BeachbotsMatt/Chassis/New Gripper Designs/GripperRedesignOne/FingerBottom.SLDPRT

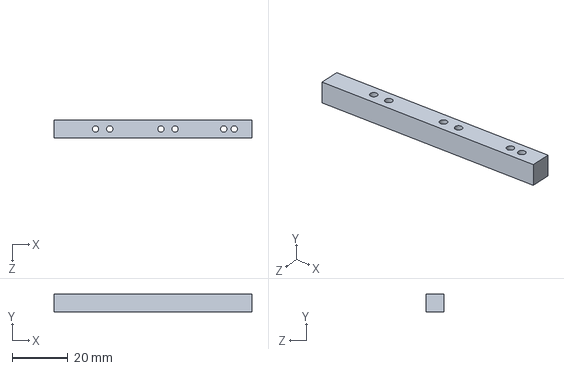
[picture p71: CAD file, 2021-03-08]
Chassis/New Gripper Designs/GripperRedesignOne/FingerBottom.SLDPRT
71.1 x 6.35 x 6.35 mm
