mklangkamp/BeachbotsMatt/Basebot Stand/StandTop.SLDPRT

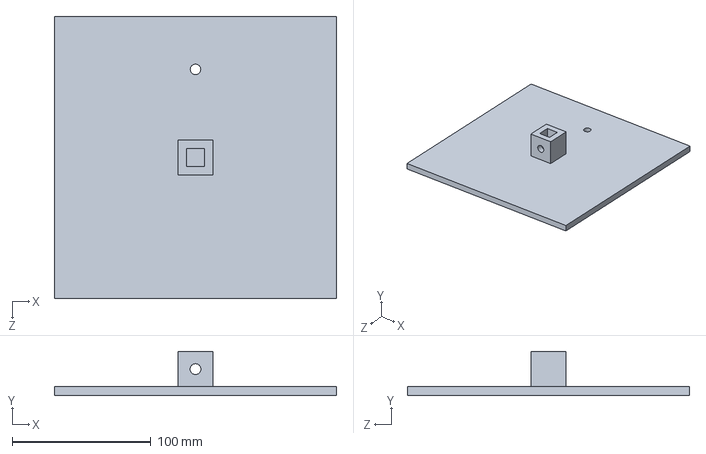
[picture p72: CAD file, 2021-02-08]
Basebot Stand/StandTop.SLDPRT
203.2 x 31.8 x 203.2 mm
