mklangkamp/BeachbotsMatt/Basebot/Short Rack Support Structure.SLDPRT

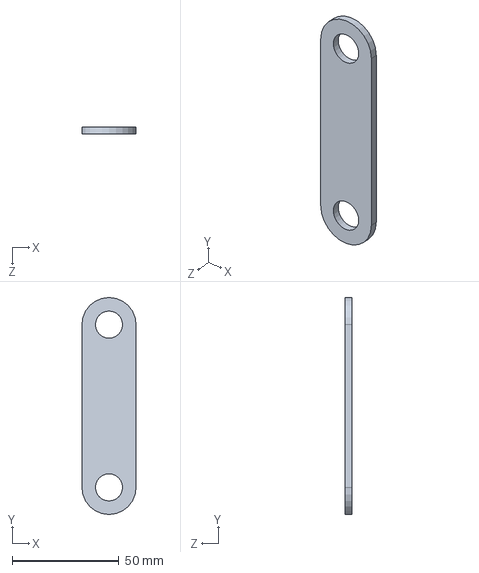
[picture p73: CAD file, 2021-05-04]
Basebot/Short Rack Support Structure.SLDPRT
25.4 x 101.6 x 3.17 mm
