mklangkamp/BeachbotsMatt/Chassis/Limit switch mount for arm.SLDPRT

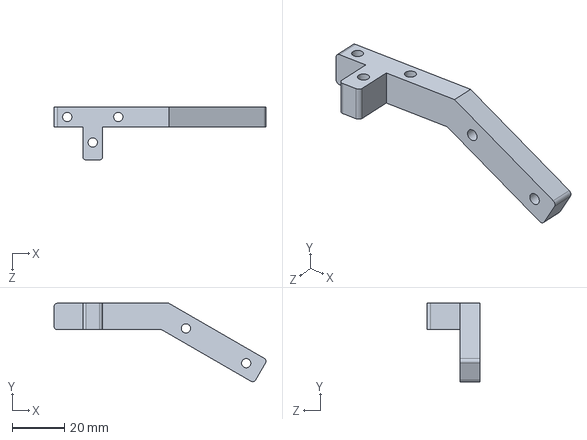
[picture p74: CAD file, 2021-01-31]
Chassis/Limit switch mount for arm.SLDPRT
81.2 x 30.1 x 20.3 mm
