mklangkamp/BeachbotsMatt/Chassis/New Gripper Designs/GripperRedesignOne/FingerTop.SLDPRT

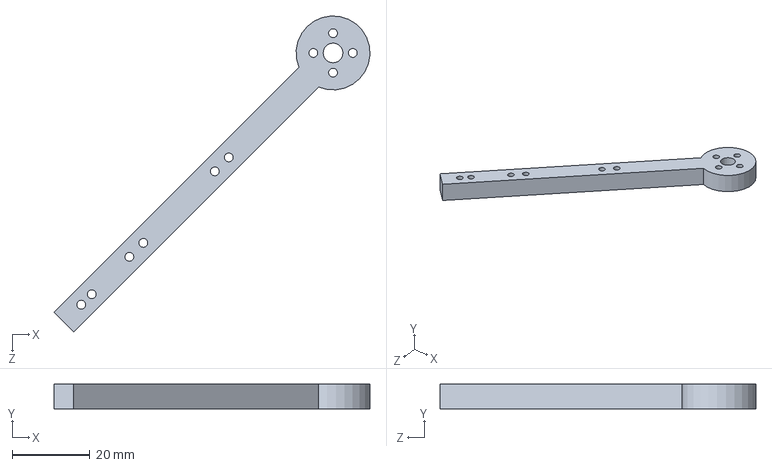
[picture p75: CAD file, 2021-03-08]
Chassis/New Gripper Designs/GripperRedesignOne/FingerTop.SLDPRT
81.4 x 6.35 x 81.4 mm
