mklangkamp/BeachbotsMatt/Basebot Stand/StandBottomLegConnector.SLDPRT

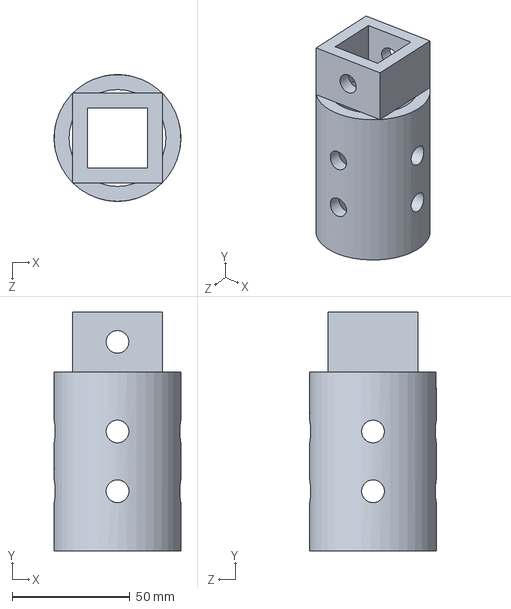
[picture p76: CAD file, 2021-02-08]
Basebot Stand/StandBottomLegConnector.SLDPRT
53.9 x 101.6 x 53.9 mm
