mklangkamp/BeachbotsMatt/Basebot/Raspberry Pi Mount.SLDPRT

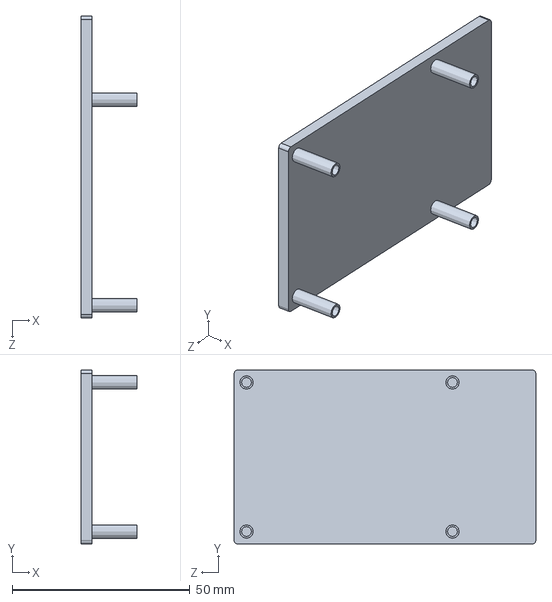
[picture p77: CAD file, 2021-05-04]
Basebot/Raspberry Pi Mount.SLDPRT
15.9 x 49.0 x 85.0 mm
