mklangkamp/BeachbotsMatt/Chassis/new bucket bracket.SLDPRT

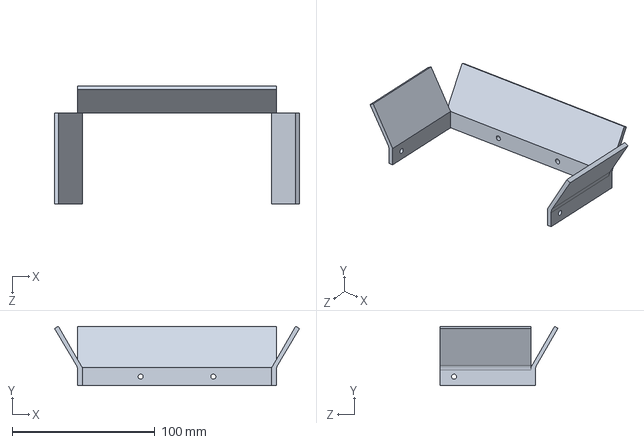
[picture p78: CAD file, 2021-01-22]
Chassis/new bucket bracket.SLDPRT
171.4 x 41.6 x 82.6 mm
