mklangkamp/BeachbotsMatt/Basebot Stand/StandBottomLeg.SLDPRT

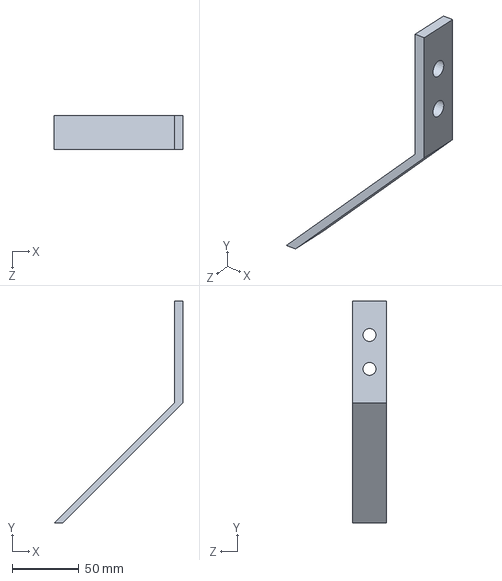
[picture p79: CAD file, 2021-02-08]
Basebot Stand/StandBottomLeg.SLDPRT
96.2 x 166.0 x 25.4 mm
