mklangkamp/BeachbotsMatt/Chassis/bucket ramp.SLDPRT

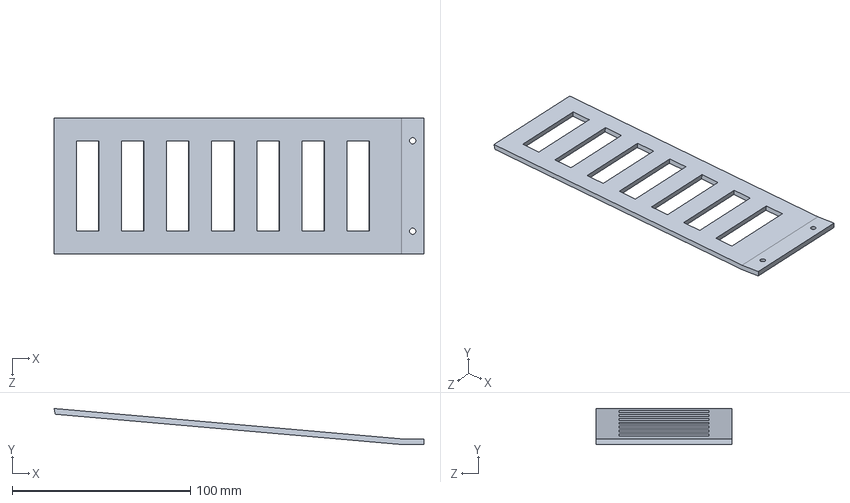
[picture p80: CAD file, 2021-01-11]
Chassis/bucket ramp.SLDPRT
207.7 x 20.2 x 76.2 mm
