mklangkamp/BeachbotsMatt/Basebot/Spacer.SLDPRT

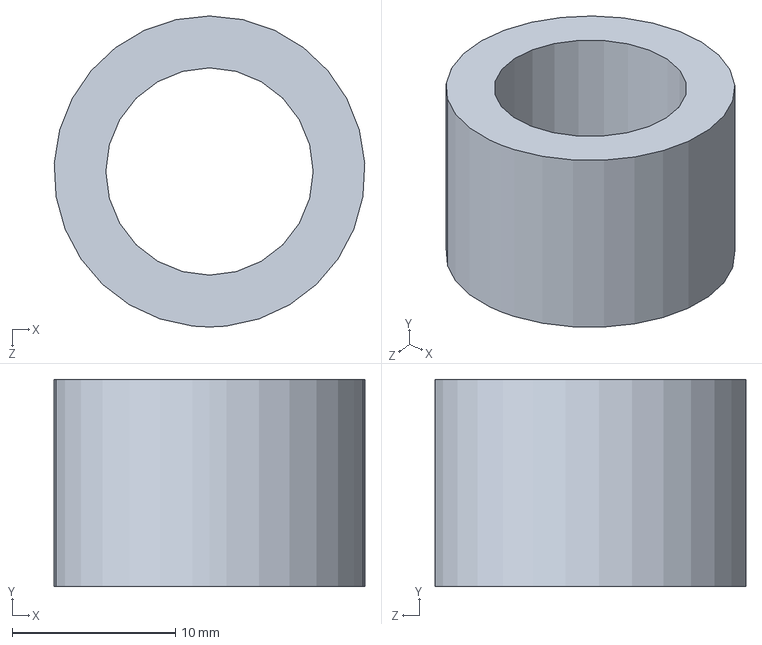
[picture p81: CAD file, 2021-05-04]
Basebot/Spacer.SLDPRT
19.0 x 12.7 x 19.1 mm
