mklangkamp/BeachbotsMatt/Chassis/Bucket Bottom Spencer v2.SLDPRT

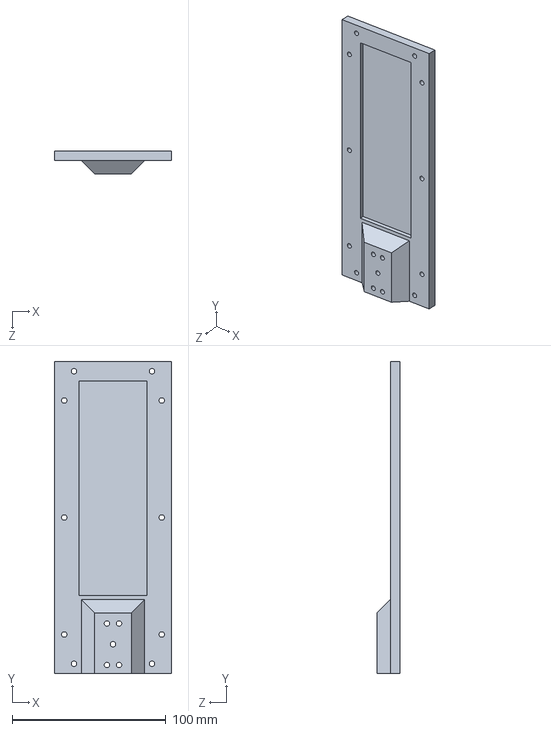
[picture p82: CAD file, 2020-12-03]
Chassis/Bucket Bottom Spencer v2.SLDPRT
76.2 x 203.2 x 15.1 mm
