mklangkamp/BeachbotsMatt/Basebot/Gearbox Lid.SLDPRT

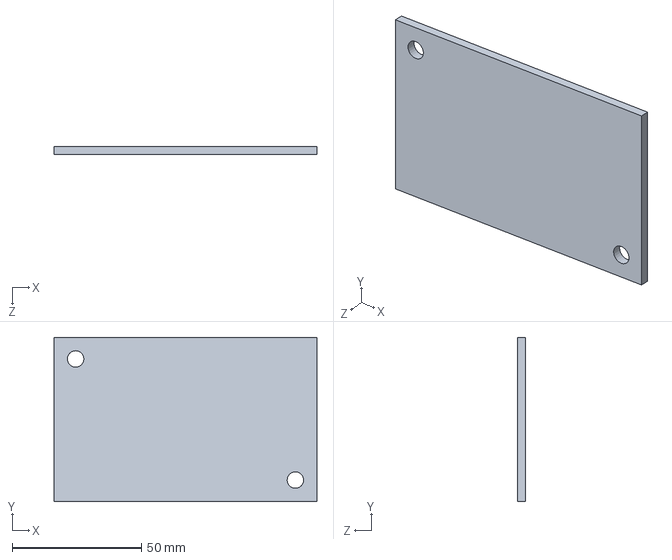
[picture p83: CAD file, 2021-05-04]
Basebot/Gearbox Lid.SLDPRT
101.6 x 63.5 x 3.17 mm
