mklangkamp/BeachbotsMatt/Chassis/voltage regulator mounts.SLDPRT

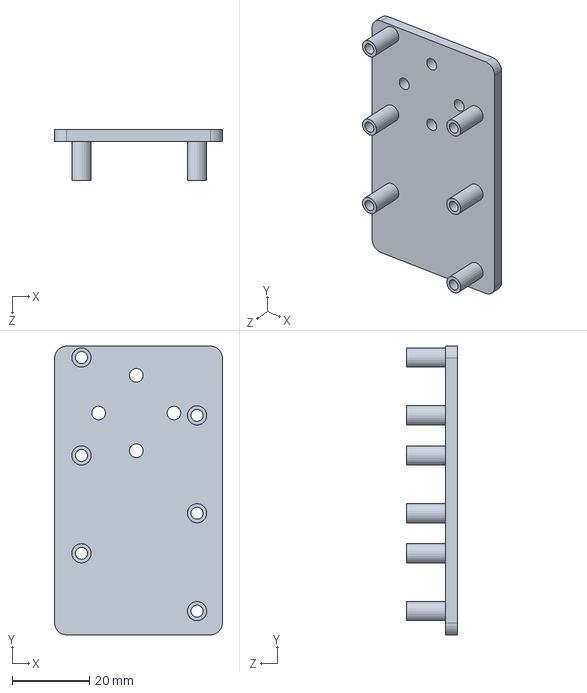
[picture p84: CAD file, 2020-12-01]
Chassis/voltage regulator mounts.SLDPRT
43.6 x 75.0 x 13.3 mm
