mklangkamp/BeachbotsMatt/Basebot/Motor to Axle Adapter.SLDPRT

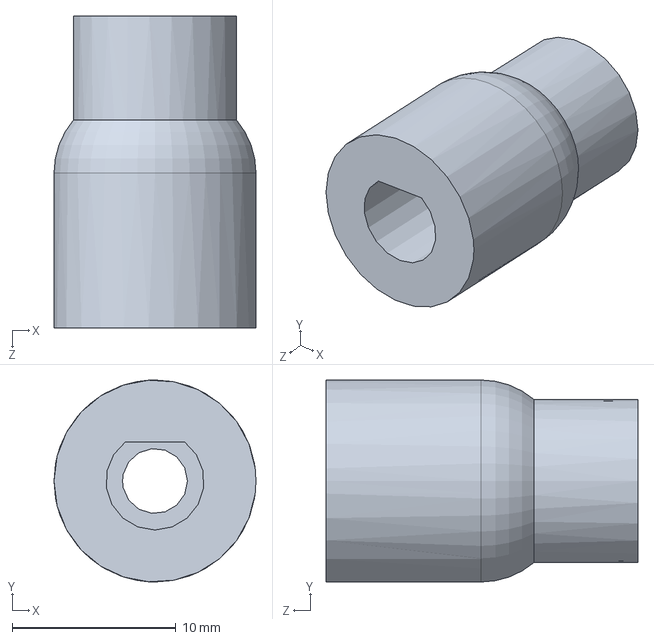
[picture p85: CAD file, 2021-05-04]
Basebot/Motor to Axle Adapter.SLDPRT
12.3 x 12.3 x 19.0 mm
