mklangkamp/BeachbotsMatt/Chassis/Servo controller and stepper driver mount 2.SLDPRT

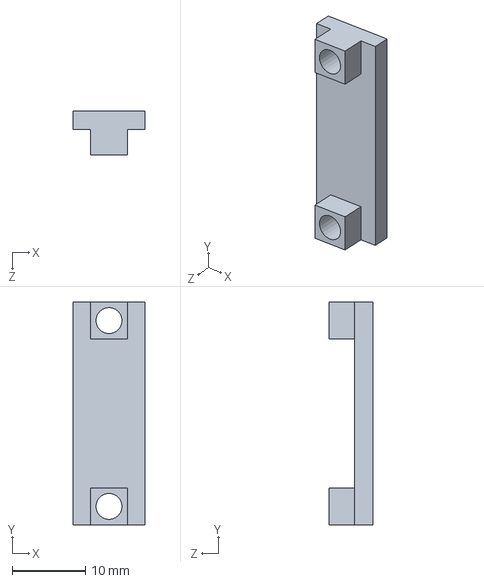
[picture p86: CAD file, 2020-11-28]
Chassis/Servo controller and stepper driver mount 2.SLDPRT
9.91 x 30.5 x 5.97 mm
