mklangkamp/BeachbotsMatt/Basebot/Hub.SLDPRT

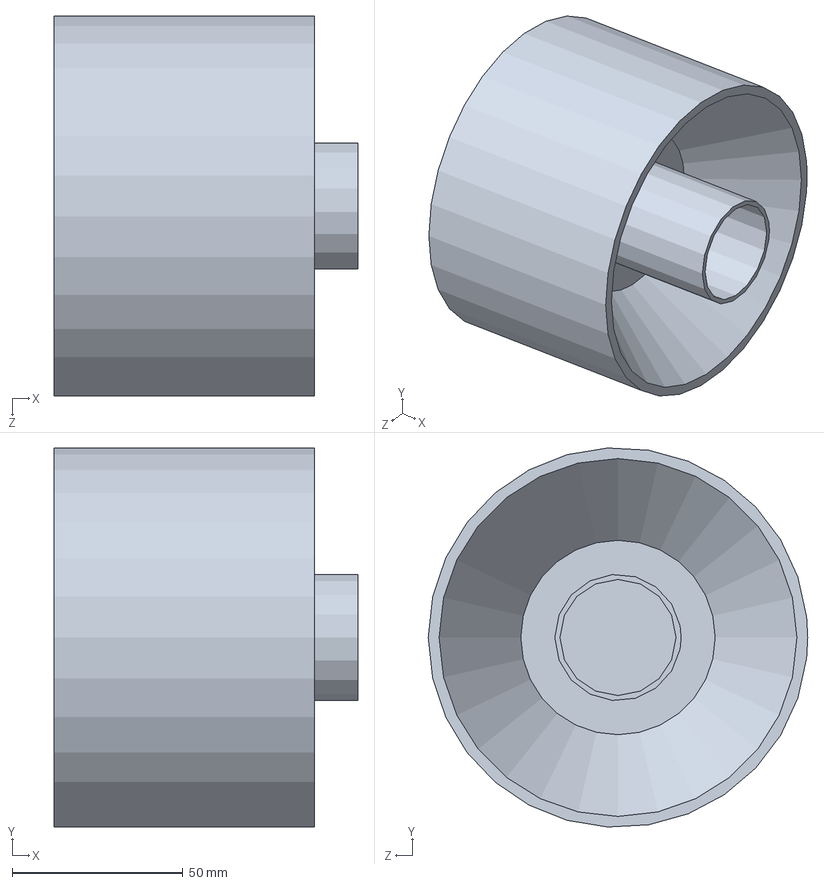
[picture p87: CAD file, 2021-05-04]
Basebot/Hub.SLDPRT
88.9 x 111.0 x 111.1 mm
