mklangkamp/BeachbotsMatt/Chassis/Servo controller and stepper driver mount.SLDPRT

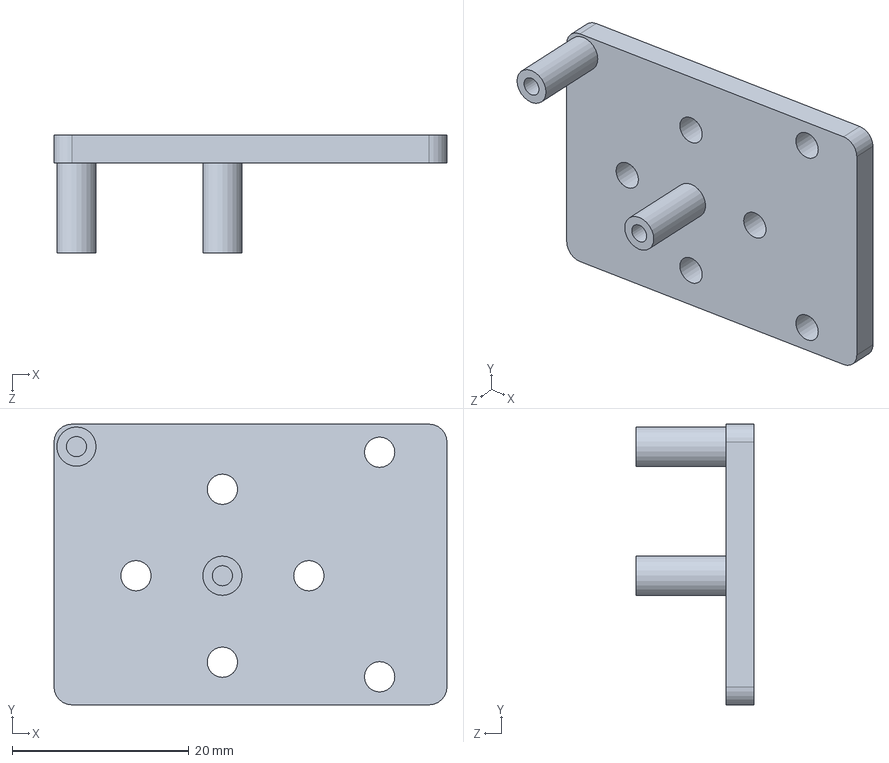
[picture p88: CAD file, 2020-11-28]
Chassis/Servo controller and stepper driver mount.SLDPRT
44.5 x 31.8 x 13.3 mm
