mklangkamp/BeachbotsMatt/Basebot/Mighty Max Battery 12V.SLDPRT

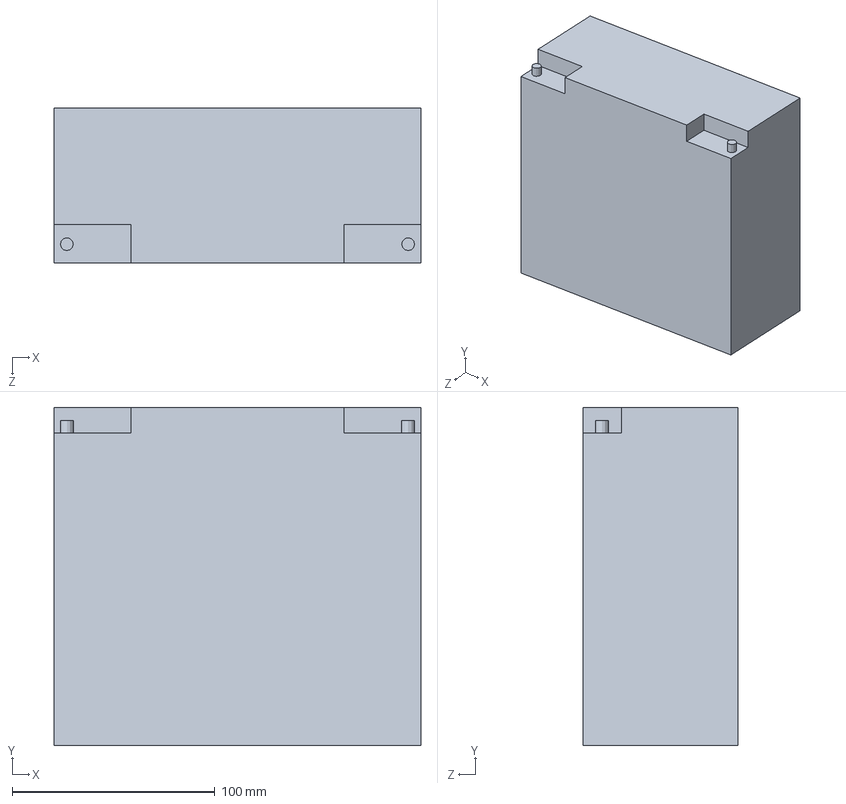
[picture p89: CAD file, 2021-05-04]
Basebot/Mighty Max Battery 12V.SLDPRT
181.1 x 166.9 x 76.5 mm
