mklangkamp/BeachbotsMatt/Chassis/Smallbot camera mount.SLDPRT

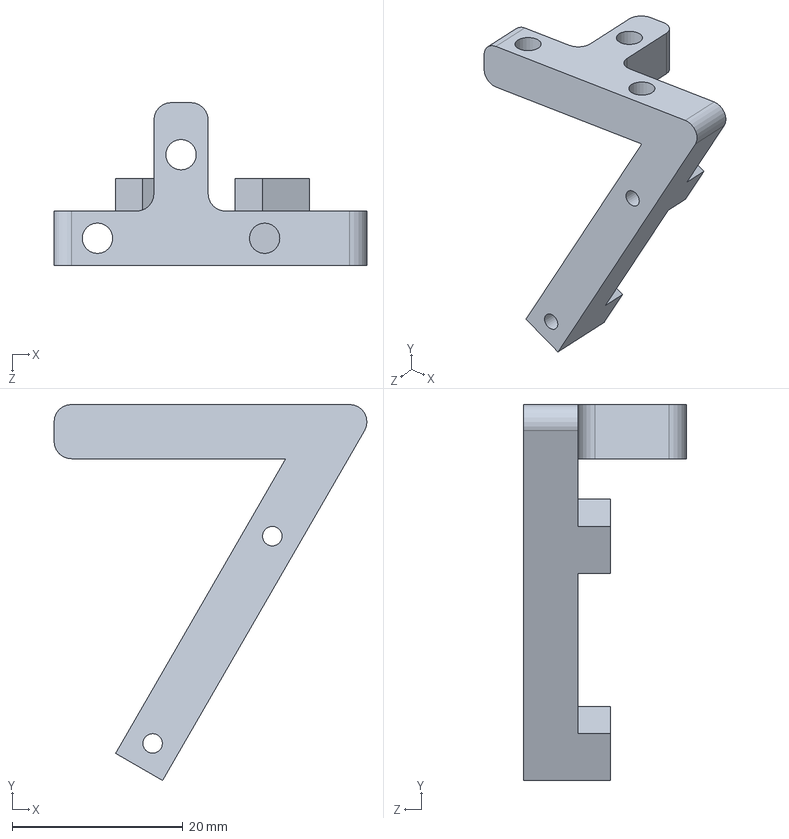
[picture p90: CAD file, 2020-11-26]
Chassis/Smallbot camera mount.SLDPRT
36.6 x 44.0 x 19.0 mm
