mklangkamp/BeachbotsMatt/Chassis/Camera Mount with Servo.SLDPRT

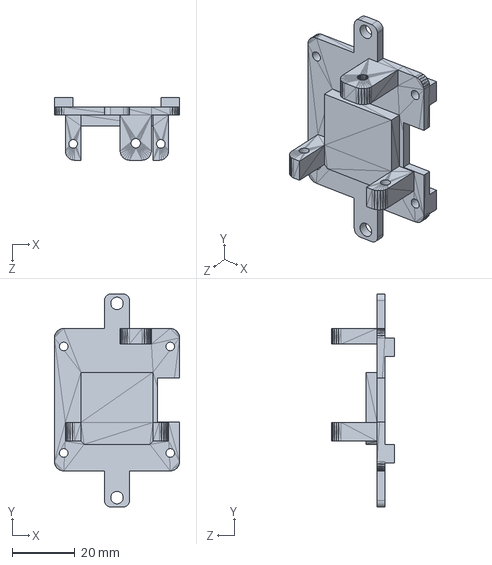
[picture p91: CAD file, 2020-11-26]
Chassis/Camera Mount with Servo.SLDPRT
40.0 x 68.0 x 20.0 mm
