mklangkamp/BeachbotsMatt/Basebot/Long Rack Support Structure (Top).SLDPRT

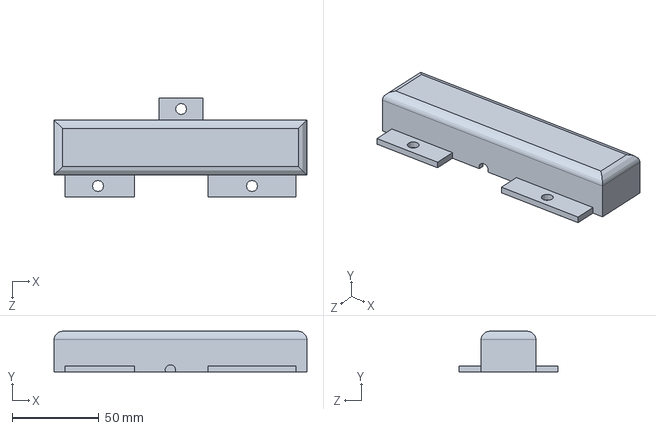
[picture p92: CAD file, 2021-05-04]
Basebot/Long Rack Support Structure (Top).SLDPRT
146.1 x 23.6 x 57.2 mm
