mklangkamp/BeachbotsMatt/Basebot/IMU Mount.SLDPRT

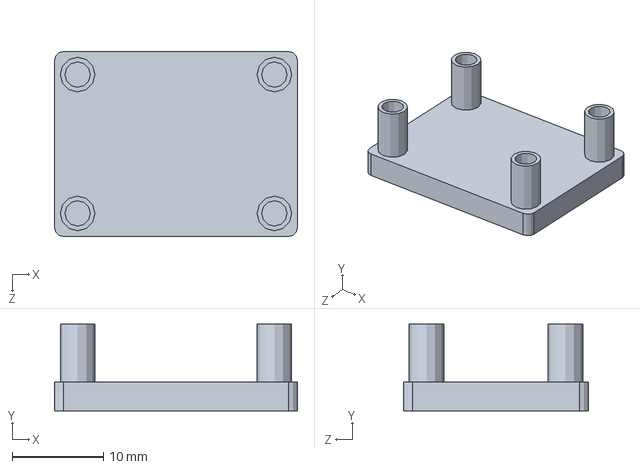
[picture p93: CAD file, 2021-05-04]
Basebot/IMU Mount.SLDPRT
26.7 x 9.53 x 20.3 mm
