mklangkamp/BeachbotsMatt/Chassis/Arm stepper motor support.SLDPRT

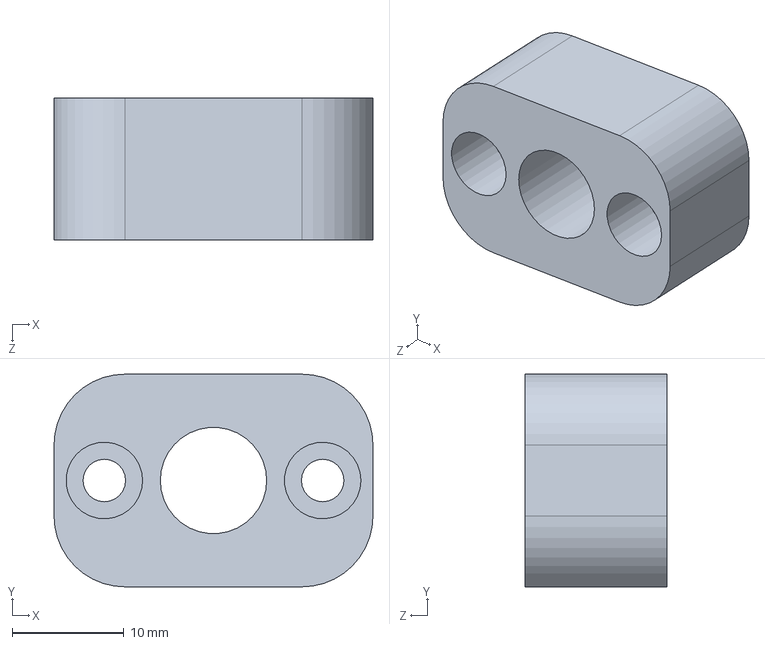
[picture p94: CAD file, 2020-11-20]
Chassis/Arm stepper motor support.SLDPRT
28.6 x 19.1 x 12.7 mm
