mklangkamp/BeachbotsMatt/Basebot/Pinon Gear.SLDPRT

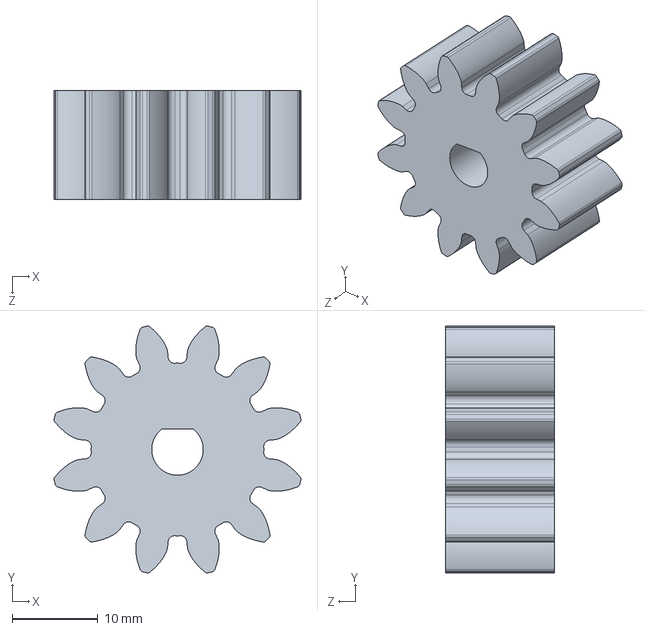
[picture p95: CAD file, 2021-05-04]
Basebot/Pinon Gear.SLDPRT
28.8 x 28.8 x 12.7 mm
