mklangkamp/BeachbotsMatt/Chassis/Arm stepper motor mount.SLDPRT

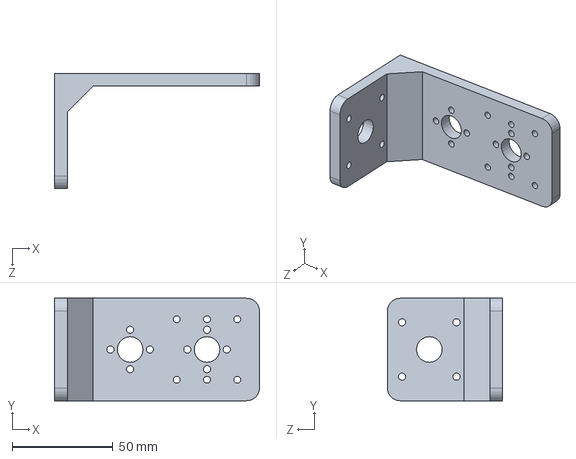
[picture p96: CAD file, 2020-11-17]
Chassis/Arm stepper motor mount.SLDPRT
101.6 x 50.8 x 57.1 mm
