mklangkamp/BeachbotsMatt/Basebot/Gearbox Support.SLDPRT

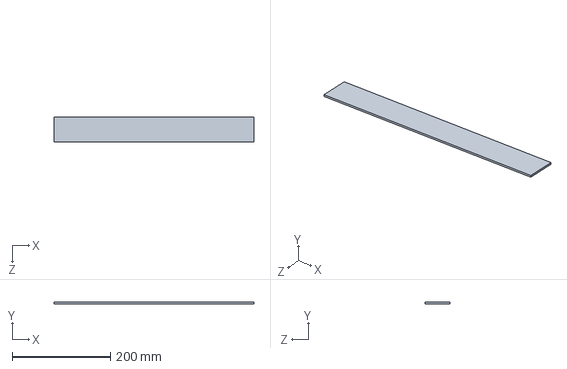
[picture p97: CAD file, 2021-05-04]
Basebot/Gearbox Support.SLDPRT
406.4 x 3.17 x 50.8 mm
