mklangkamp/BeachbotsMatt/Basebot/Long Rack Support Structure.SLDPRT

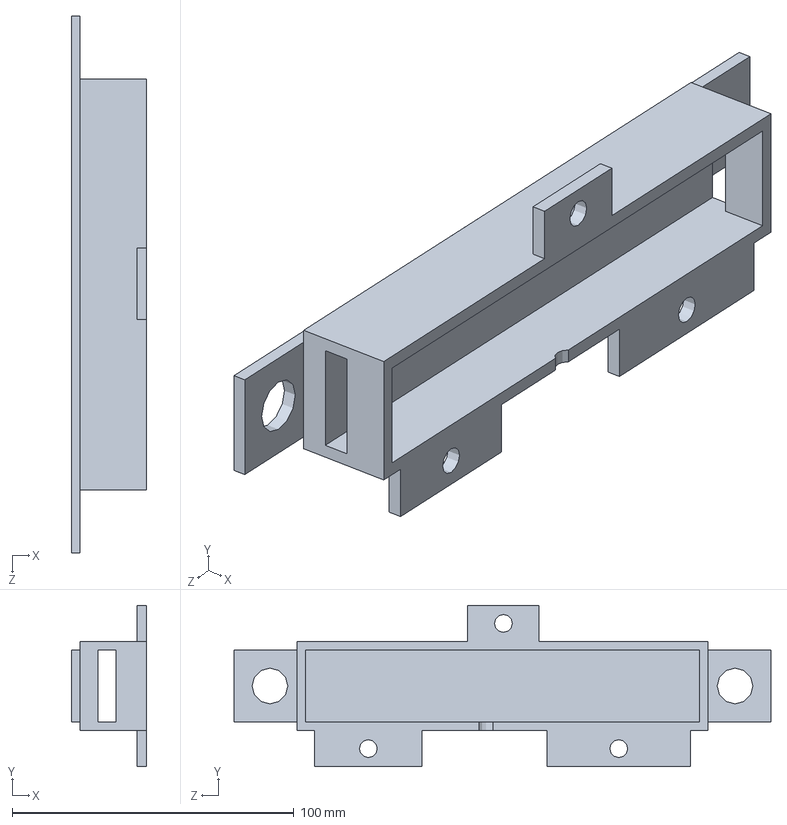
[picture p98: CAD file, 2021-05-04]
Basebot/Long Rack Support Structure.SLDPRT
26.8 x 57.2 x 190.5 mm
