mklangkamp/BeachbotsMatt/Chassis/1.75in standoff post.SLDPRT

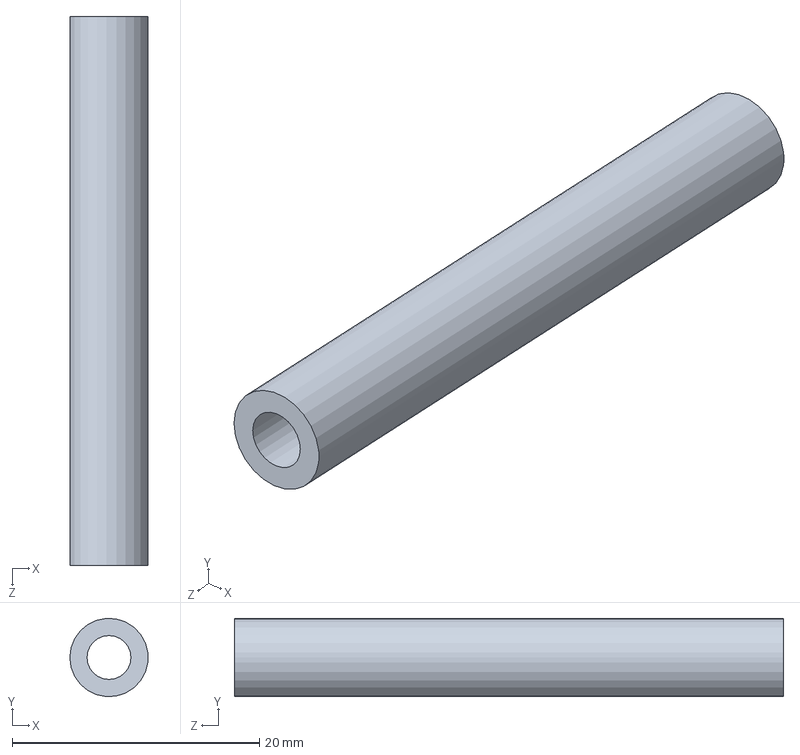
[picture p99: CAD file, 2020-11-16]
Chassis/1.75in standoff post.SLDPRT
6.35 x 6.34 x 44.5 mm
