mklangkamp/BeachbotsMatt/Basebot/Front Wheel Support.SLDPRT

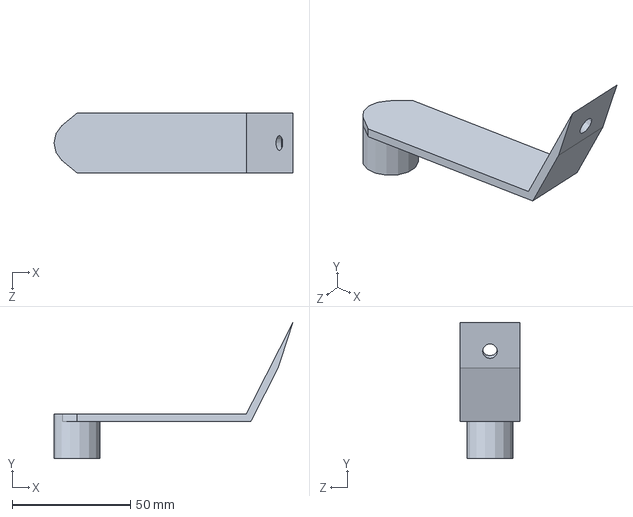
[picture p100: CAD file, 2021-05-04]
Basebot/Front Wheel Support.SLDPRT
101.1 x 57.7 x 25.4 mm
