mklangkamp/BeachbotsMatt/Chassis/bucket mount.SLDPRT

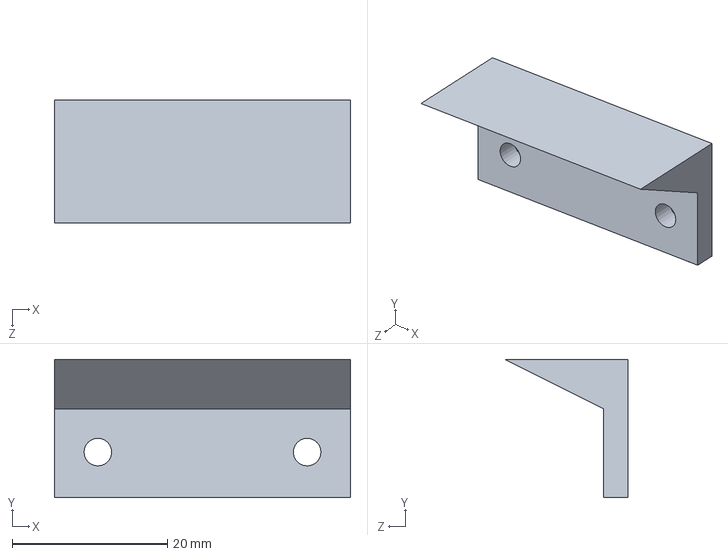
[picture p101: CAD file, 2020-11-16]
Chassis/bucket mount.SLDPRT
38.1 x 17.8 x 15.9 mm
