mklangkamp/BeachbotsMatt/Basebot/Front Wheel Brace.SLDPRT

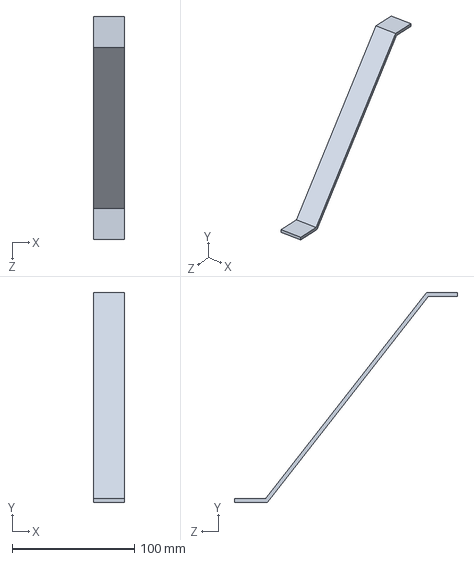
[picture p102: CAD file, 2021-05-04]
Basebot/Front Wheel Brace.SLDPRT
25.4 x 171.5 x 182.3 mm
