mklangkamp/BeachbotsMatt/Chassis/Bucket side wall 1.SLDPRT

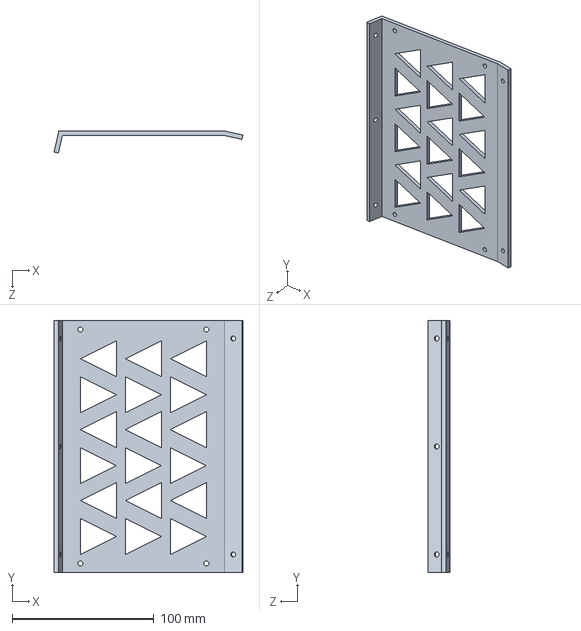
[picture p103: CAD file, 2020-11-16]
Chassis/Bucket side wall 1.SLDPRT
133.3 x 177.8 x 15.6 mm
