mklangkamp/BeachbotsMatt/Basebot/Front Wheel Axles.SLDPRT

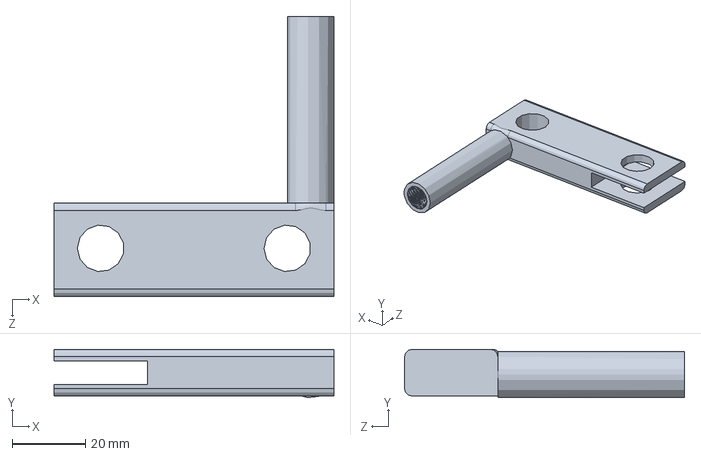
[picture p104: CAD file, 2021-05-04]
Basebot/Front Wheel Axles.SLDPRT
76.2 x 13.1 x 76.2 mm
