mklangkamp/BeachbotsMatt/Chassis/Bucket side wall 2.SLDPRT

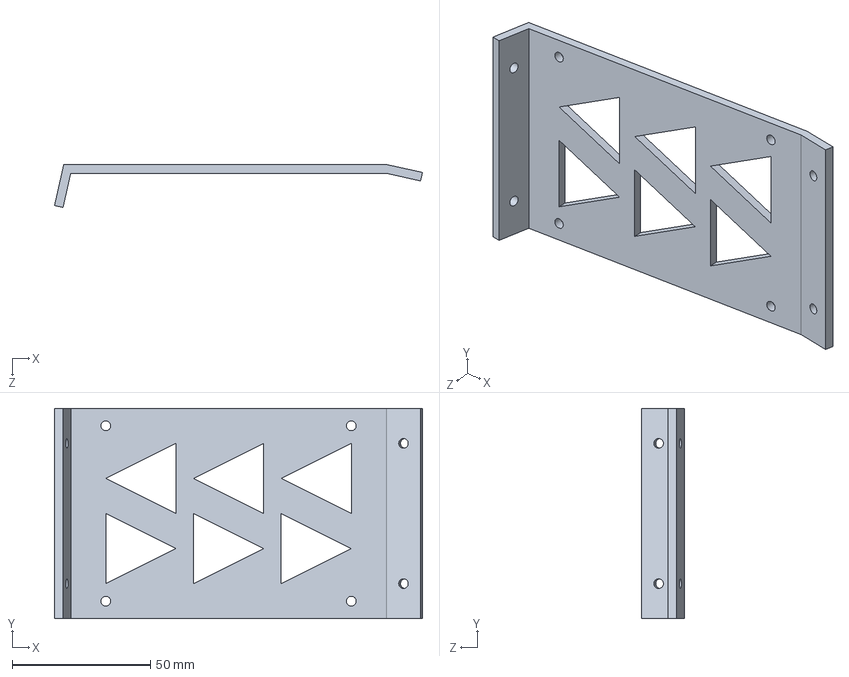
[picture p105: CAD file, 2020-11-16]
Chassis/Bucket side wall 2.SLDPRT
133.3 x 76.2 x 15.6 mm
