mklangkamp/BeachbotsMatt/Basebot/Gearbox - 24T.SLDPRT

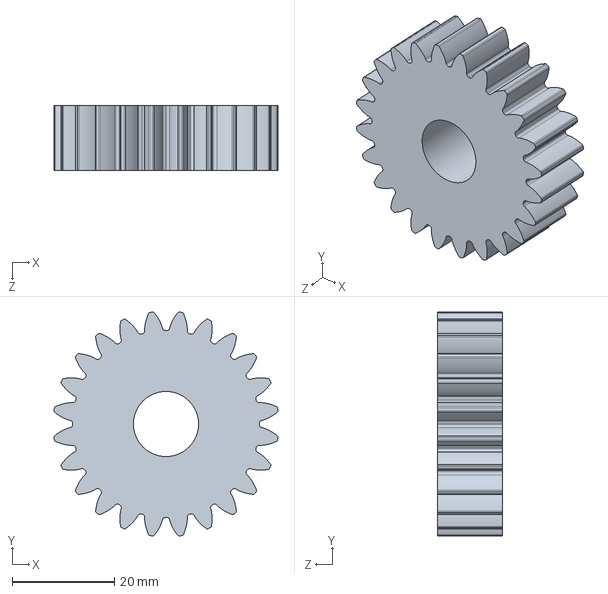
[picture p106: CAD file, 2021-05-04]
Basebot/Gearbox - 24T.SLDPRT
43.7 x 43.7 x 12.7 mm
