mklangkamp/BeachbotsMatt/Chassis/bucket bracket.SLDPRT

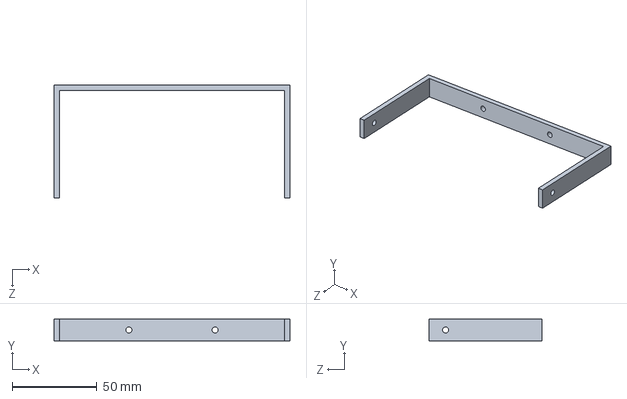
[picture p107: CAD file, 2020-11-16]
Chassis/bucket bracket.SLDPRT
138.9 x 12.7 x 66.7 mm
