mklangkamp/BeachbotsMatt/Basebot/Gearbox Bottom.SLDPRT

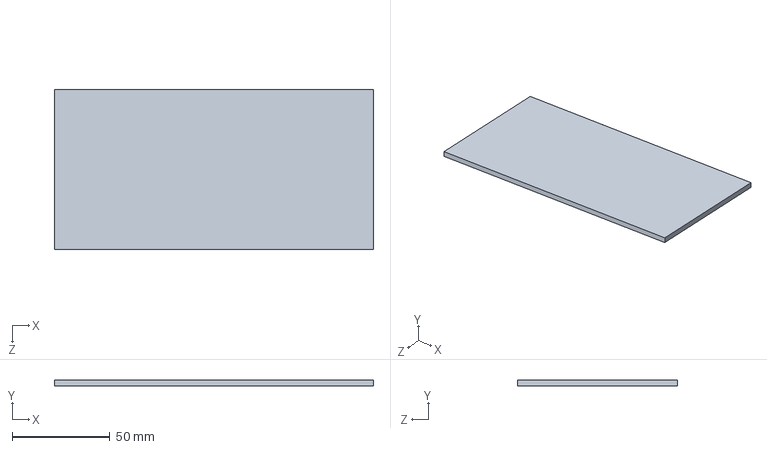
[picture p108: CAD file, 2021-05-04]
Basebot/Gearbox Bottom.SLDPRT
163.1 x 3.17 x 81.5 mm
