mklangkamp/BeachbotsMatt/Basebot/Front Wheel Bracket.SLDPRT

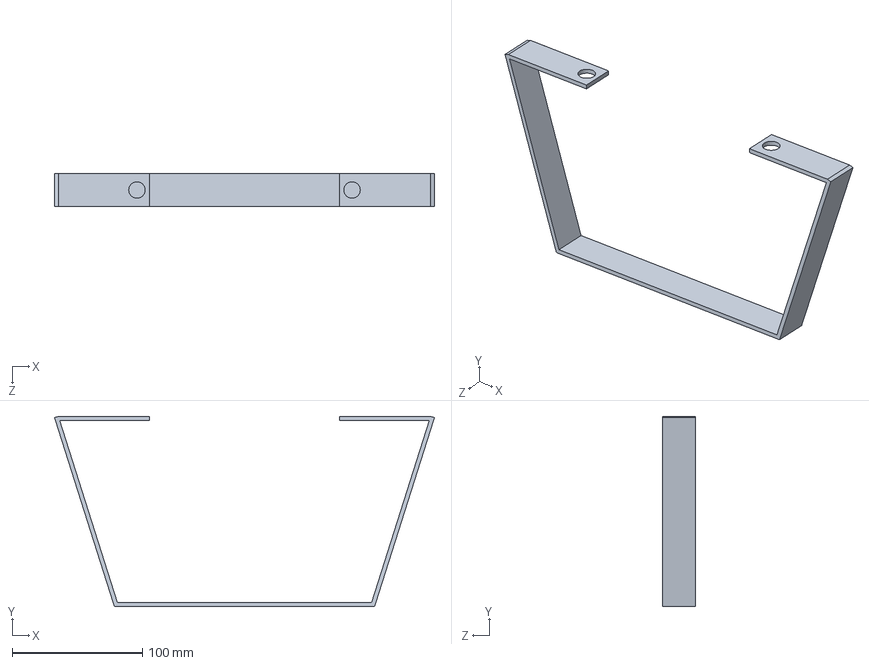
[picture p109: CAD file, 2021-05-04]
Basebot/Front Wheel Bracket.SLDPRT
292.1 x 146.2 x 25.4 mm
