mklangkamp/BeachbotsMatt/Chassis/6.16in 17 hole Beam (585416).SLDPRT

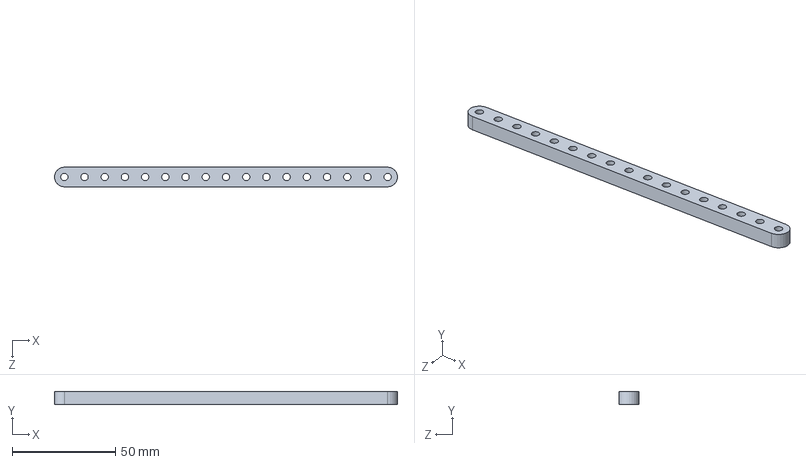
[picture p110: CAD file, 2020-11-15]
Chassis/6.16in 17 hole Beam (585416).SLDPRT
166.0 x 6.35 x 9.53 mm
