mklangkamp/BeachbotsMatt/Chassis/Side Tapped Pattern Mount A - 545420.SLDPRT

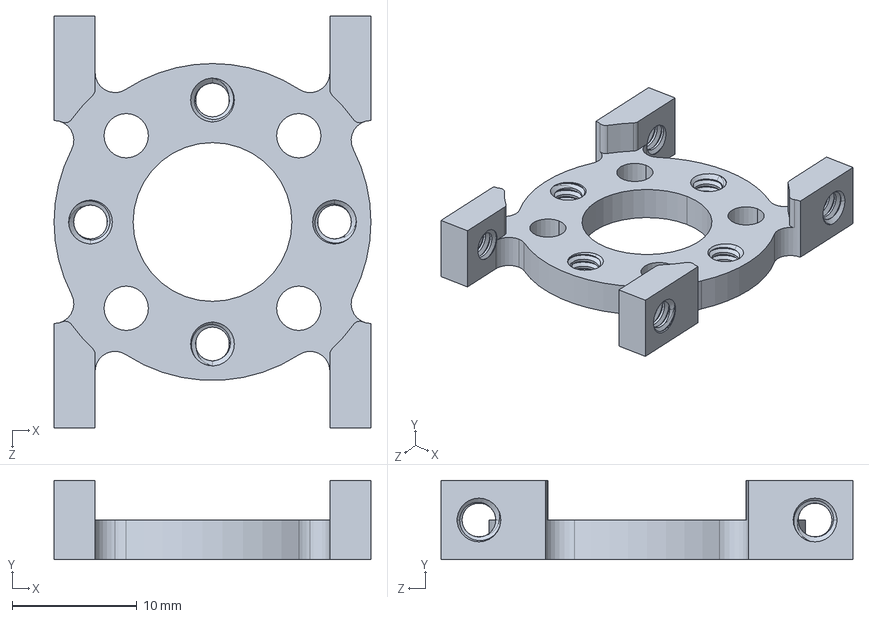
[picture p111: CAD file, 2020-11-15]
Chassis/Side Tapped Pattern Mount A - 545420.SLDPRT
25.4 x 6.35 x 33.0 mm
