mklangkamp/BeachbotsMatt/Basebot/Control Arm.SLDPRT

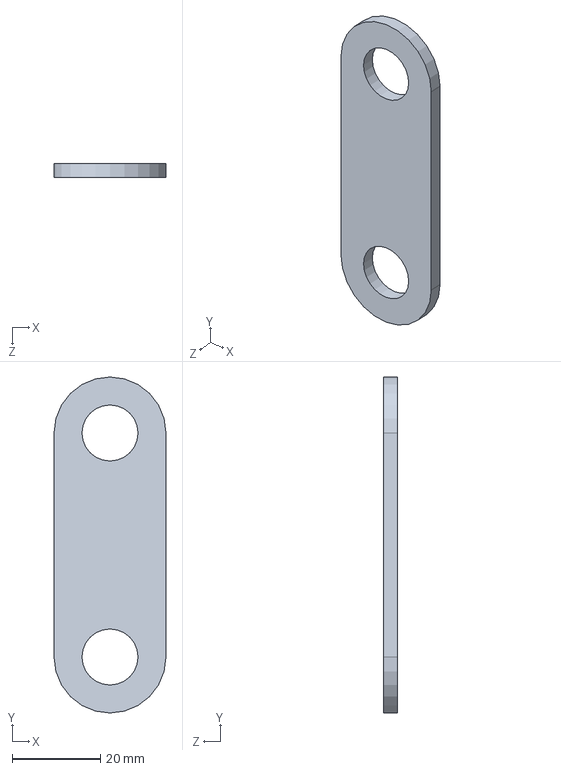
[picture p112: CAD file, 2021-05-04]
Basebot/Control Arm.SLDPRT
25.4 x 76.2 x 3.17 mm
