mklangkamp/BeachbotsMatt/Chassis/90 Degree Angle Short Pattern Bracket - 585506.SLDPRT

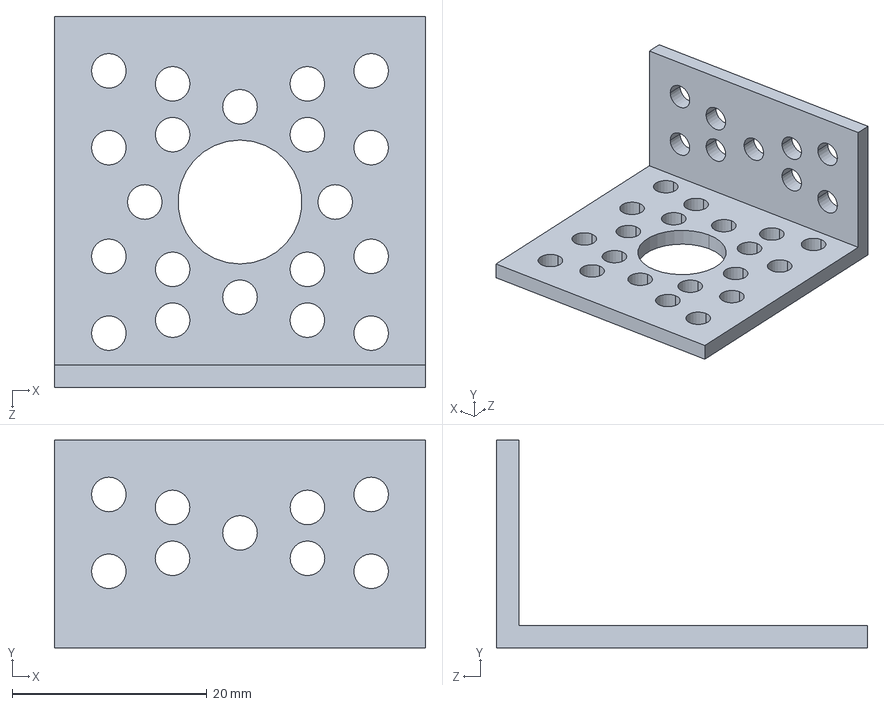
[picture p113: CAD file, 2020-11-15]
Chassis/90 Degree Angle Short Pattern Bracket - 585506.SLDPRT
38.1 x 21.3 x 38.1 mm
