mklangkamp/BeachbotsMatt/Basebot/Gearbox - 12T.SLDPRT

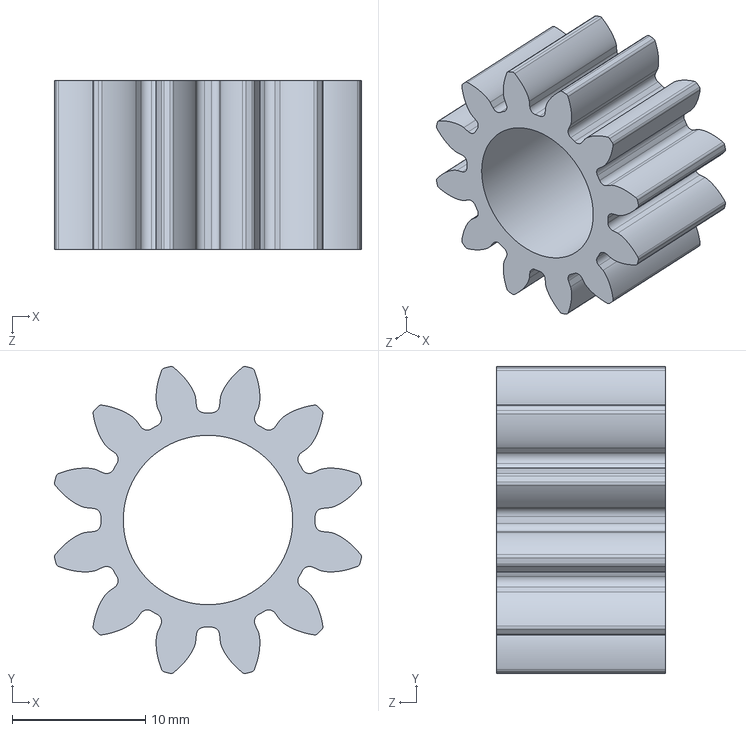
[picture p114: CAD file, 2021-05-04]
Basebot/Gearbox - 12T.SLDPRT
23.0 x 23.0 x 12.7 mm
