mklangkamp/BeachbotsMatt/Chassis/4.62in 13 hole Beam (585412).SLDPRT

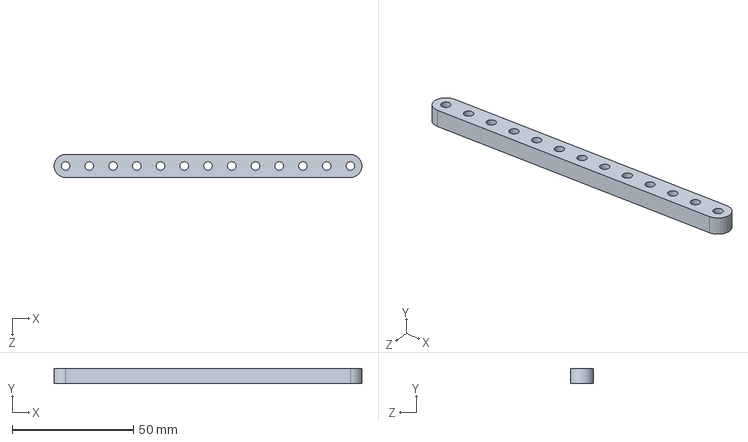
[picture p115: CAD file, 2020-11-15]
Chassis/4.62in 13 hole Beam (585412).SLDPRT
126.9 x 6.35 x 9.53 mm
