mklangkamp/BeachbotsMatt/Basebot/Electronic Housing  Lid.SLDPRT

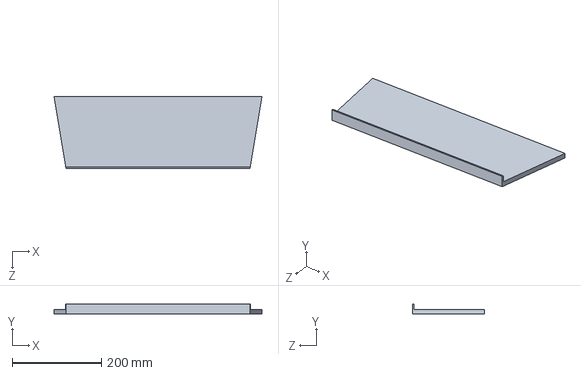
[picture p116: CAD file, 2021-05-04]
Basebot/Electronic Housing Lid.SLDPRT
466.7 x 22.7 x 160.8 mm
