mklangkamp/BeachbotsMatt/Basebot/Electronic Housing.SLDPRT

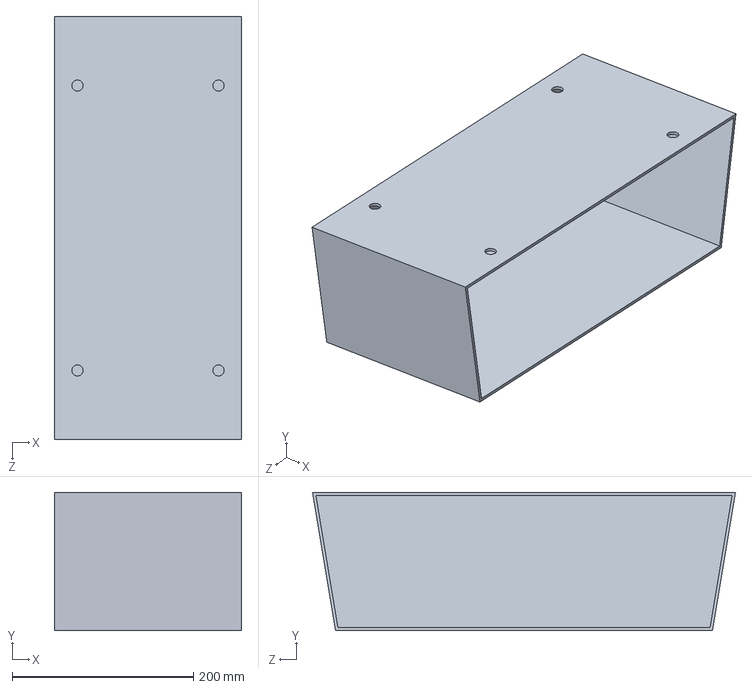
[picture p117: CAD file, 2021-05-04]
Basebot/Electronic Housing.SLDPRT
206.4 x 152.4 x 466.7 mm
