mklangkamp/BeachbotsMatt/Chassis/Standard Servo Plate A (575112).SLDPRT

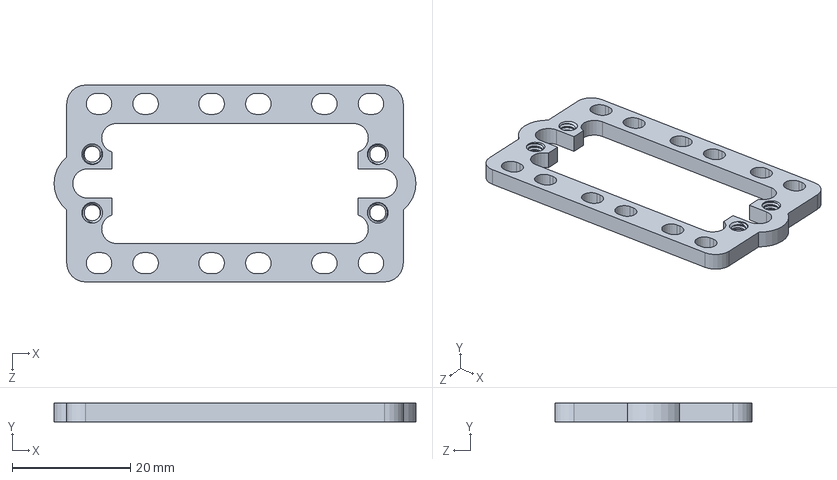
[picture p118: CAD file, 2020-11-15]
Chassis/Standard Servo Plate A (575112).SLDPRT
61.2 x 3.17 x 33.3 mm
