mklangkamp/BeachbotsMatt/Basebot/Basket Side.SLDPRT

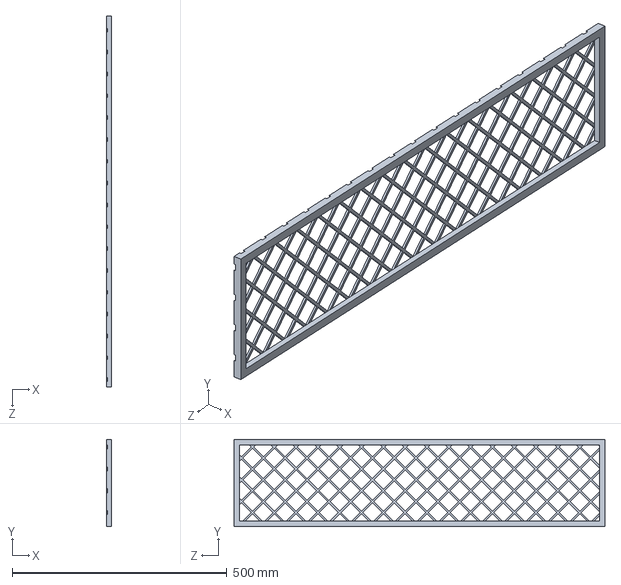
[picture p119: CAD file, 2021-05-04]
Basebot/Basket Side.SLDPRT
12.7 x 203.2 x 863.6 mm
