mklangkamp/BeachbotsMatt/Chassis/Side Tapped Pattern Mount C - 545360.SLDPRT

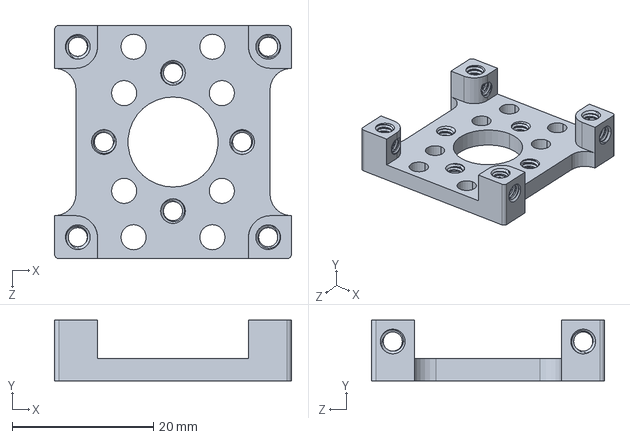
[picture p120: CAD file, 2020-11-15]
Chassis/Side Tapped Pattern Mount C - 545360.SLDPRT
33.5 x 8.63 x 33.0 mm
