mklangkamp/BeachbotsMatt/Basebot/Basket Bottom.SLDPRT

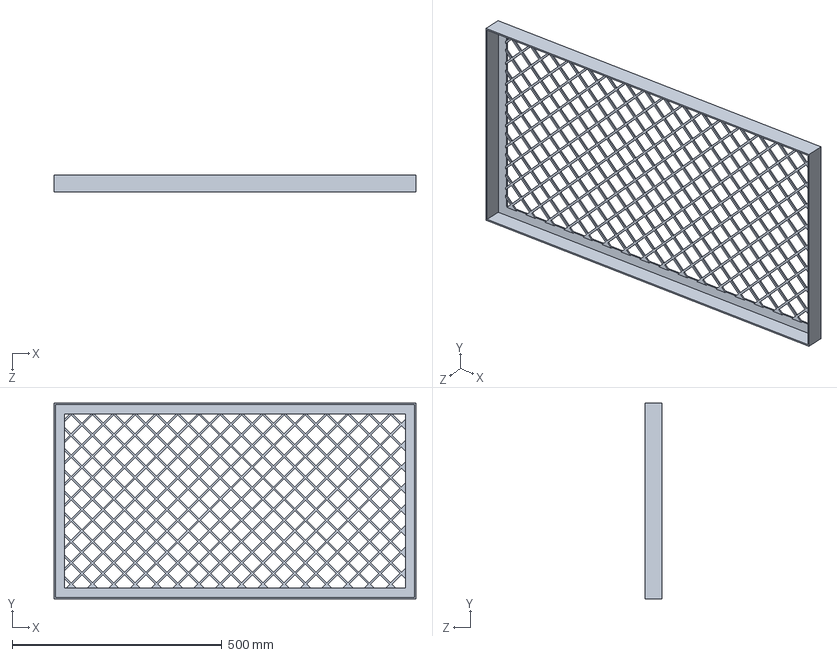
[picture p121: CAD file, 2021-05-04]
Basebot/Basket Bottom.SLDPRT
863.6 x 466.7 x 41.3 mm
