mklangkamp/BeachbotsMatt/Chassis/Clamping 8mm hub (545624).SLDPRT

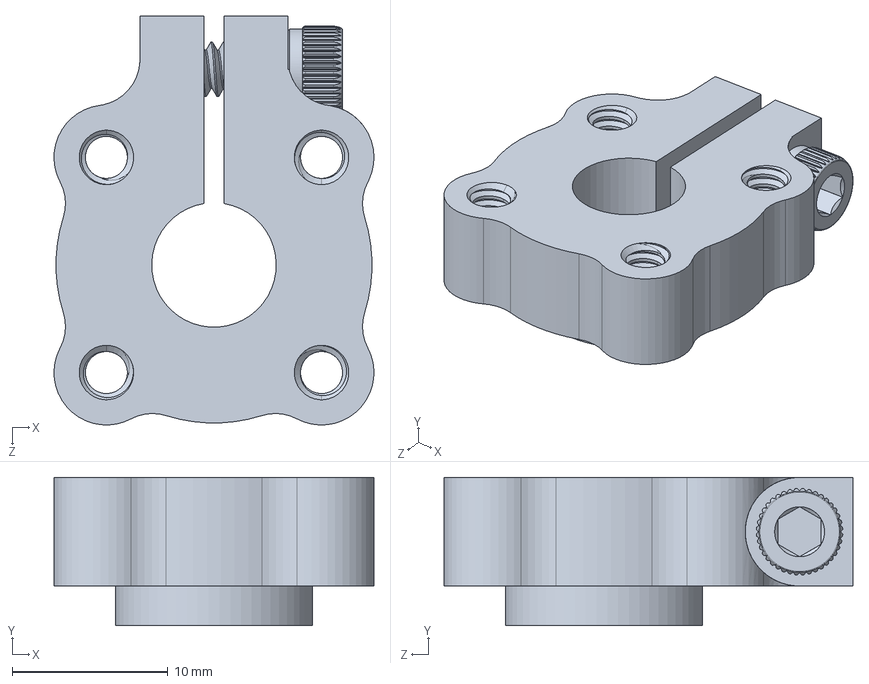
[picture p122: CAD file, 2020-11-15]
Chassis/Clamping 8mm hub (545624).SLDPRT
20.6 x 9.52 x 26.3 mm
