mklangkamp/BeachbotsMatt/Basebot/Back Wheel Support.SLDPRT

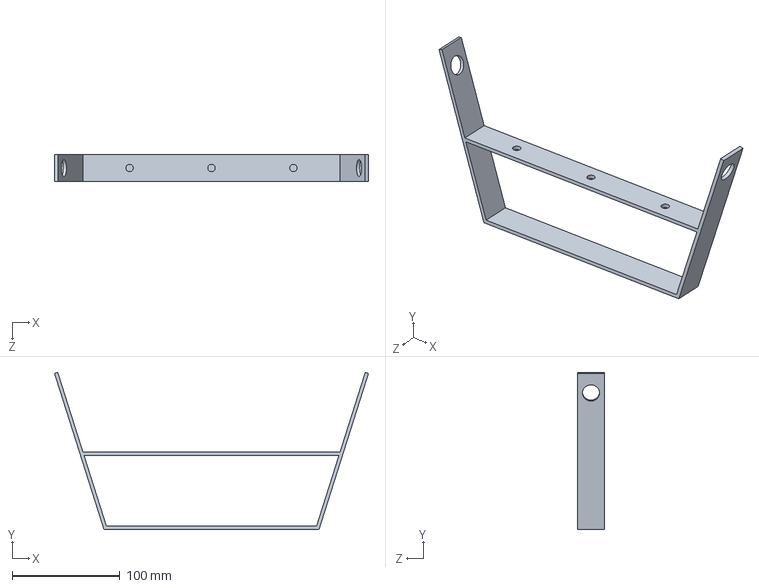
[picture p123: CAD file, 2021-05-04]
Basebot/Back Wheel Support.SLDPRT
292.1 x 146.2 x 25.4 mm
