mklangkamp/BeachbotsMatt/Chassis/Servo Hub Shafts 25T (525123).SLDPRT

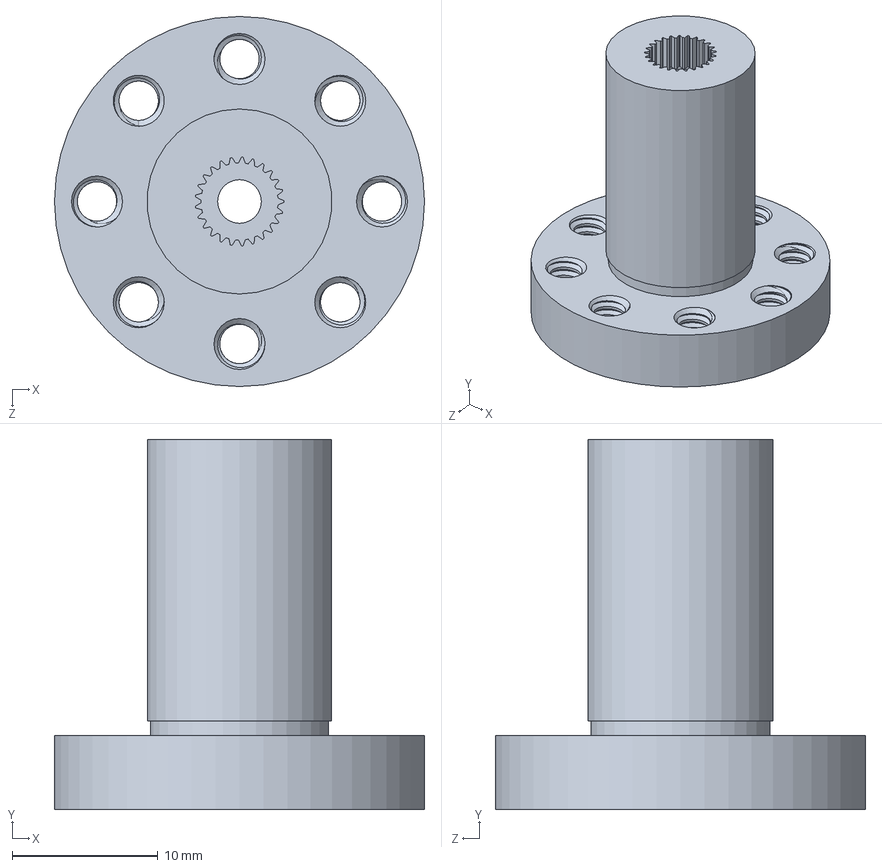
[picture p124: CAD file, 2020-11-15]
Chassis/Servo Hub Shafts 25T (525123).SLDPRT
25.4 x 25.4 x 25.4 mm
