mklangkamp/BeachbotsMatt/Basebot/2in Axle.SLDPRT

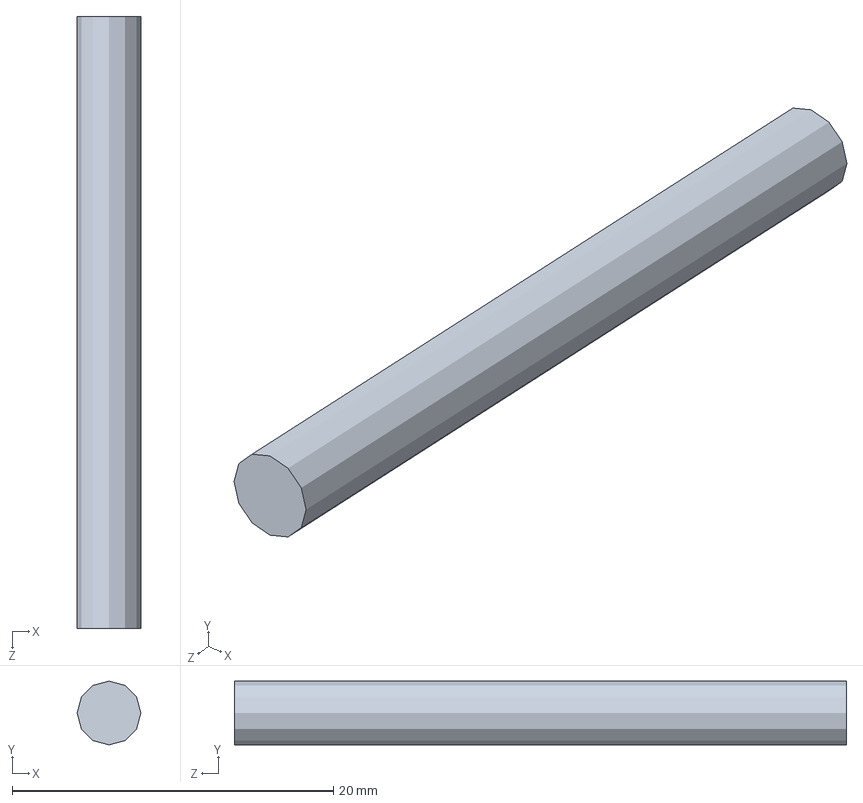
[picture p125: CAD file, 2021-05-04]
Basebot/2in Axle.SLDPRT
3.97 x 3.97 x 38.1 mm
