mklangkamp/BeachbotsMatt/Chassis/battery holder door.SLDPRT

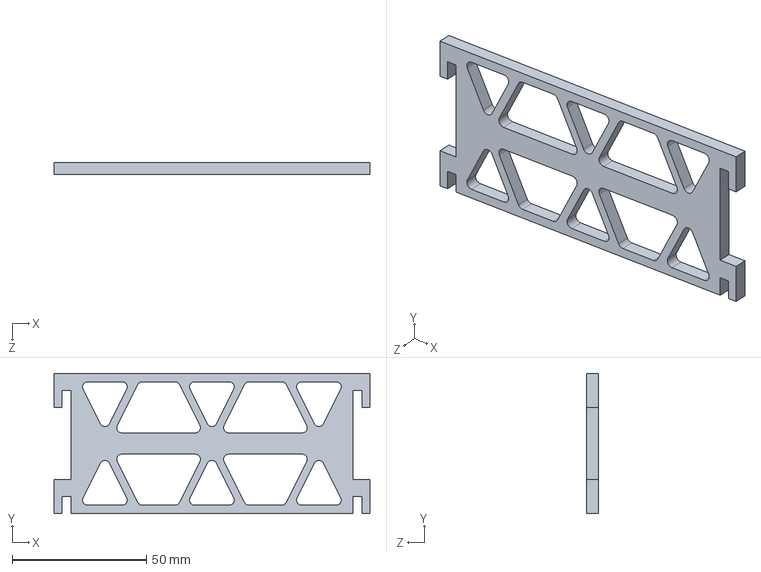
[picture p126: CAD file, 2020-11-14]
Chassis/battery holder door.SLDPRT
117.9 x 52.4 x 4.51 mm
