mklangkamp/BeachbotsMatt/Chassis/StepperMotor.SLDPRT

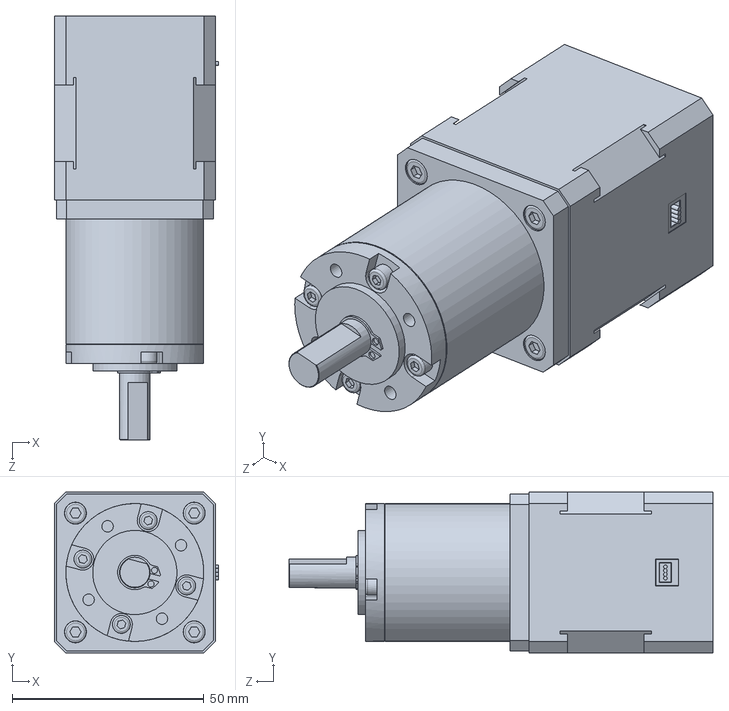
[picture p127: CAD file, 2020-11-14]
Chassis/StepperMotor.SLDPRT
42.9 x 42.0 x 110.7 mm
