mklangkamp/BeachbotsMatt/Chassis/.34in spacer for suspension.SLDPRT

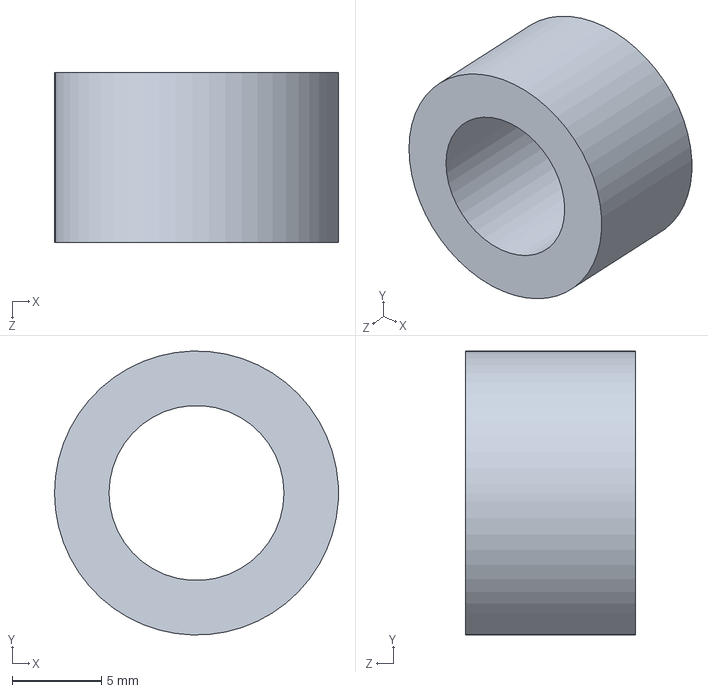
[picture p128: CAD file, 2020-11-14]
Chassis/.34in spacer for suspension.SLDPRT
15.9 x 15.9 x 9.53 mm
