mklangkamp/BeachbotsMatt/Basebot/Back Motor Housing #2.SLDPRT

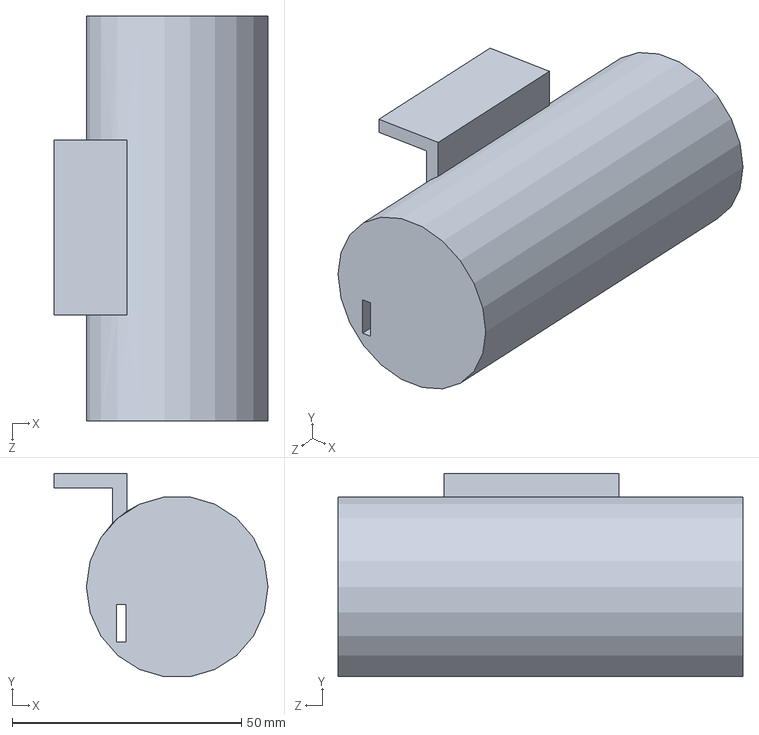
[picture p129: CAD file, 2021-05-04]
Basebot/Back Motor Housing #2.SLDPRT
46.6 x 44.3 x 88.2 mm
