mklangkamp/BeachbotsMatt/Chassis/top plate spacer.SLDPRT

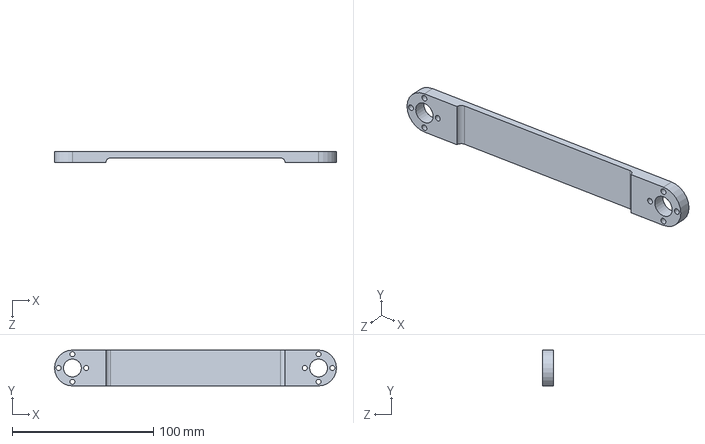
[picture p130: CAD file, 2020-11-14]
Chassis/top plate spacer.SLDPRT
199.9 x 25.4 x 7.62 mm
