mklangkamp/BeachbotsMatt/Basebot/Basket Back.SLDPRT

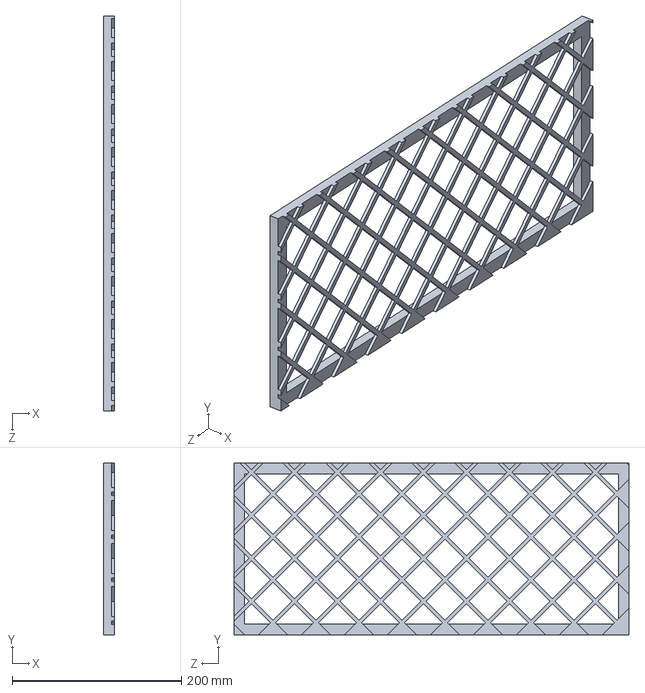
[picture p131: CAD file, 2021-05-04]
Basebot/Basket Back.SLDPRT
12.7 x 203.2 x 466.7 mm
