mklangkamp/BeachbotsMatt/Chassis/Stepper_Motor_Mount.SLDPRT

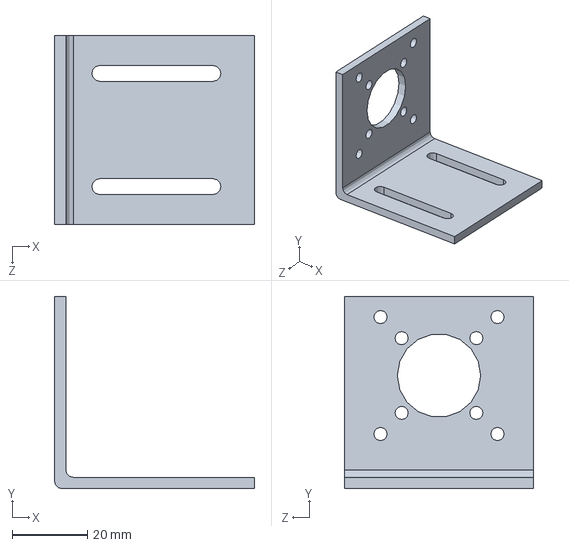
[picture p132: CAD file, 2020-11-14]
Chassis/Stepper_Motor_Mount.SLDPRT
53.0 x 51.0 x 50.0 mm
