mklangkamp/BeachbotsMatt/Basebot/1in Axle.SLDPRT

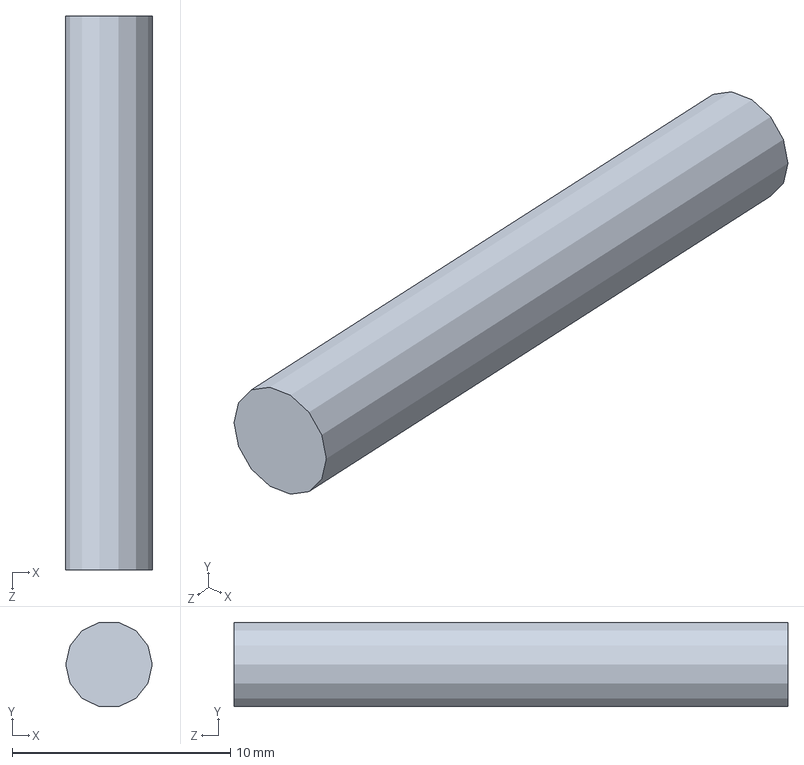
[picture p133: CAD file, 2021-05-04]
Basebot/1in Axle.SLDPRT
3.97 x 3.87 x 25.4 mm
