mklangkamp/BeachbotsMatt/Chassis/.5in x .125in thick spacer.SLDPRT

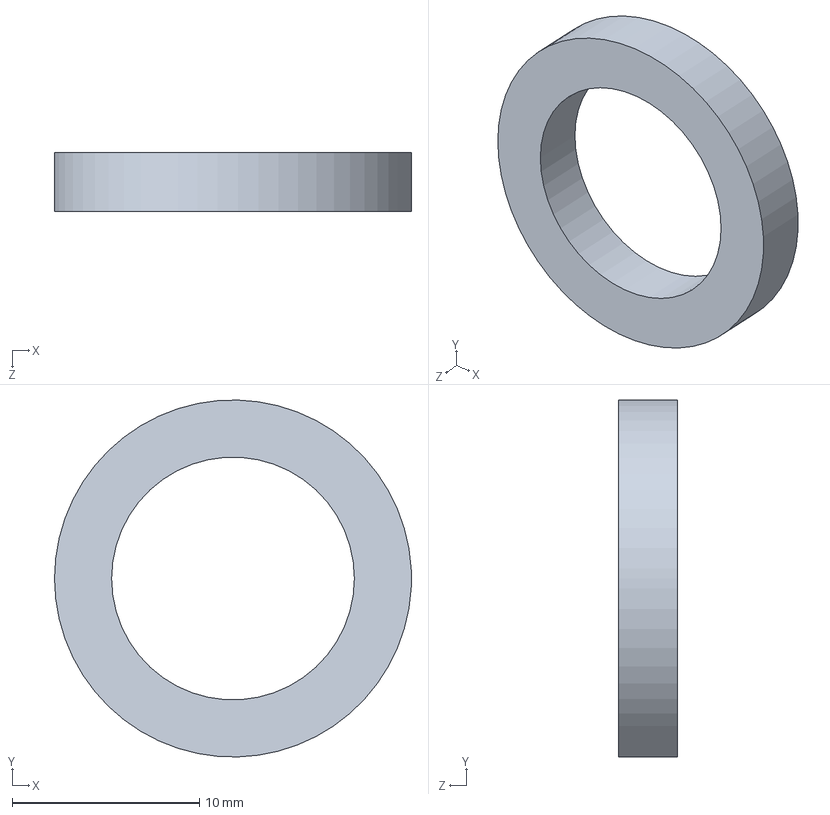
[picture p134: CAD file, 2020-11-14]
Chassis/.5in x .125in thick spacer.SLDPRT
19.1 x 19.0 x 3.17 mm
