mklangkamp/BeachbotsMatt/Basebot/Back Wheel Housing.SLDPRT

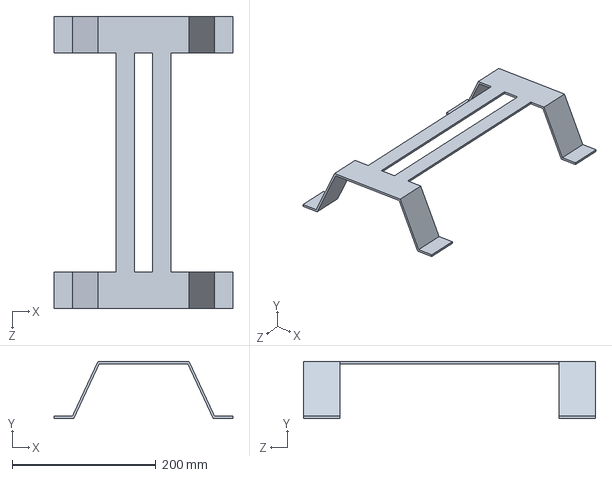
[picture p135: CAD file, 2021-05-04]
Basebot/Back Wheel Housing.SLDPRT
248.9 x 79.4 x 406.4 mm
