mklangkamp/BeachbotsMatt/Chassis/top piece spacer.SLDPRT

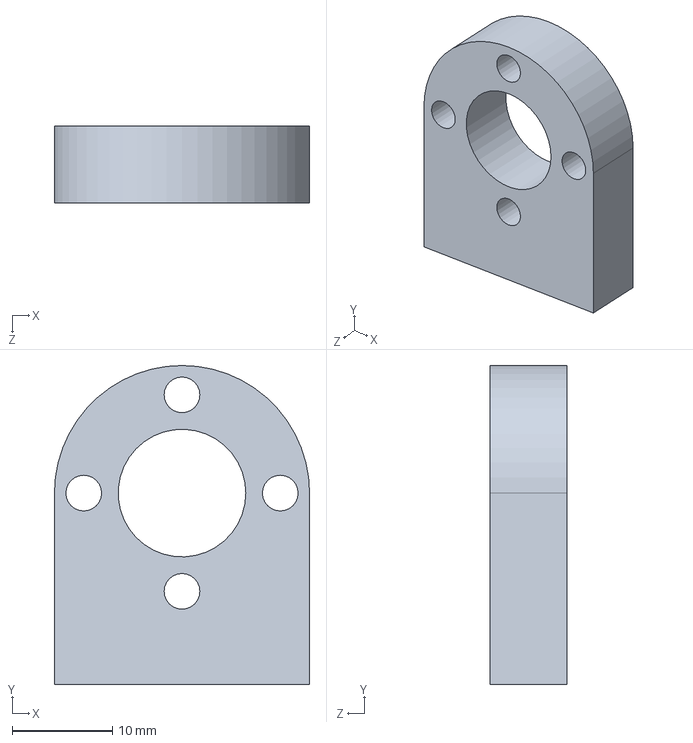
[picture p136: CAD file, 2020-11-12]
Chassis/top piece spacer.SLDPRT
25.4 x 31.8 x 7.62 mm
