mklangkamp/BeachbotsMatt/Basebot/Basket Front.SLDPRT

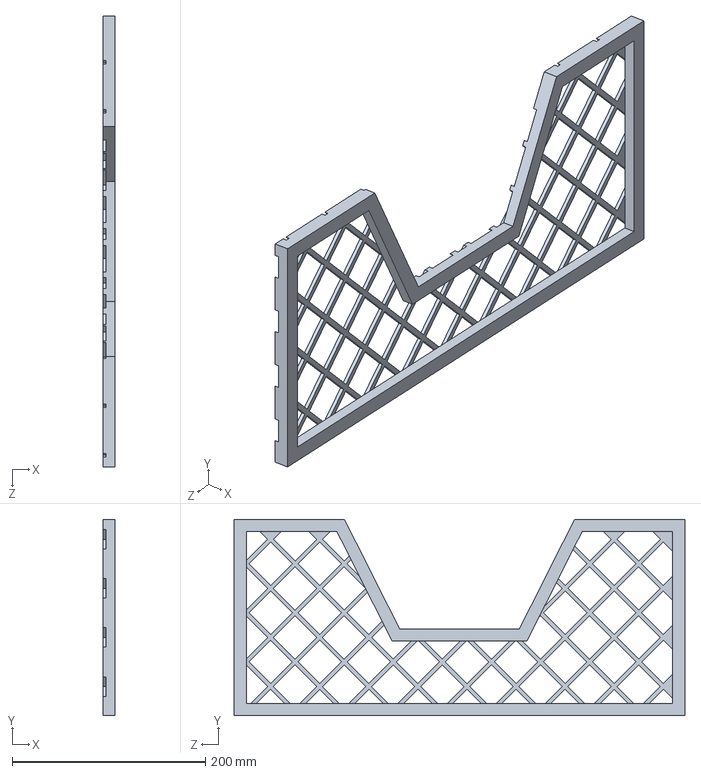
[picture p137: CAD file, 2021-05-04]
Basebot/Basket Front.SLDPRT
12.7 x 203.2 x 466.7 mm
