mklangkamp/BeachbotsMatt/Chassis/12V 16Ah Battery.SLDPRT

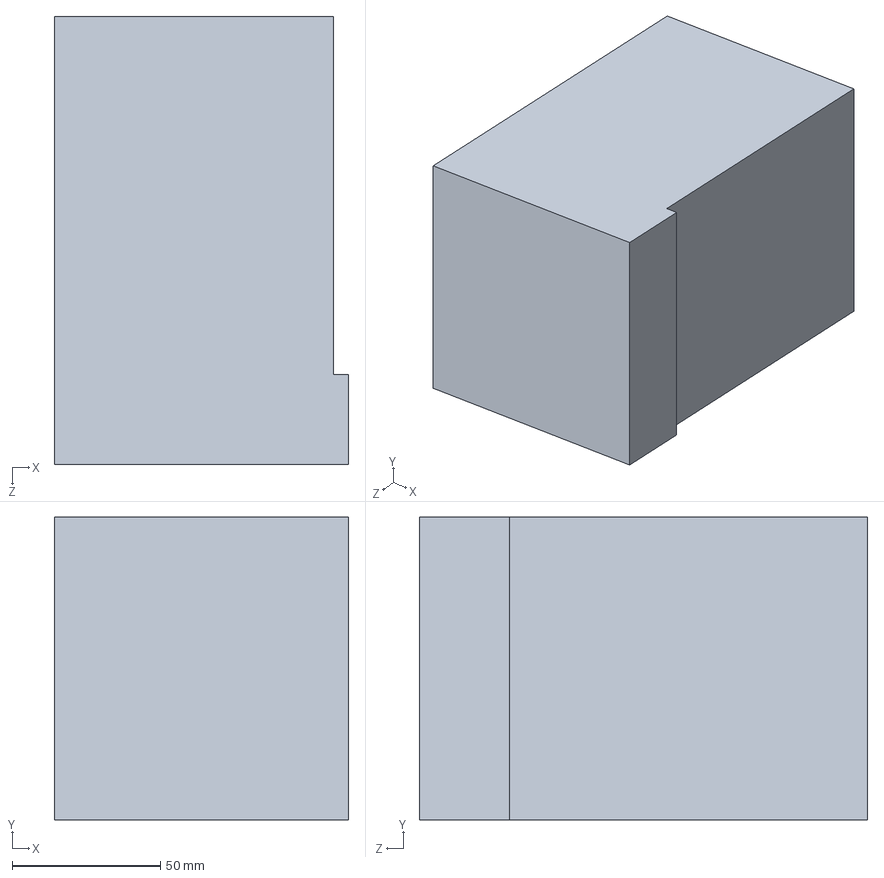
[picture p138: CAD file, 2020-11-12]
Chassis/12V 16Ah Battery.SLDPRT
99.0 x 102.0 x 151.0 mm
