mklangkamp/BeachbotsMatt/Chassis/Bucket - Top.SLDPRT

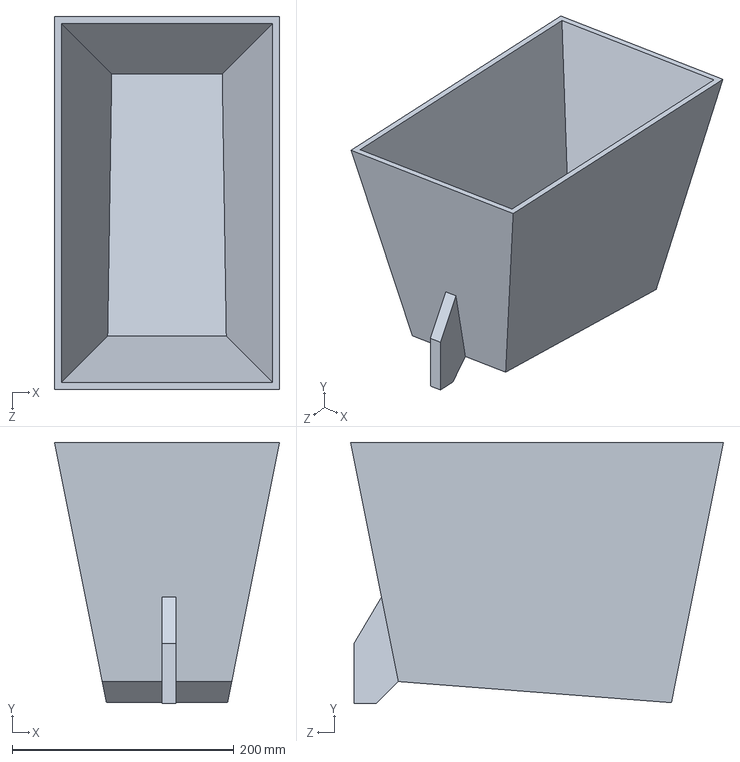
[picture p139: CAD file, 2020-11-12]
Chassis/Bucket - Top.SLDPRT
203.2 x 235.9 x 336.5 mm
