mklangkamp/BeachbotsMatt/Basebot/37d-gearmotor-100-131-150-encoder.SLDPRT

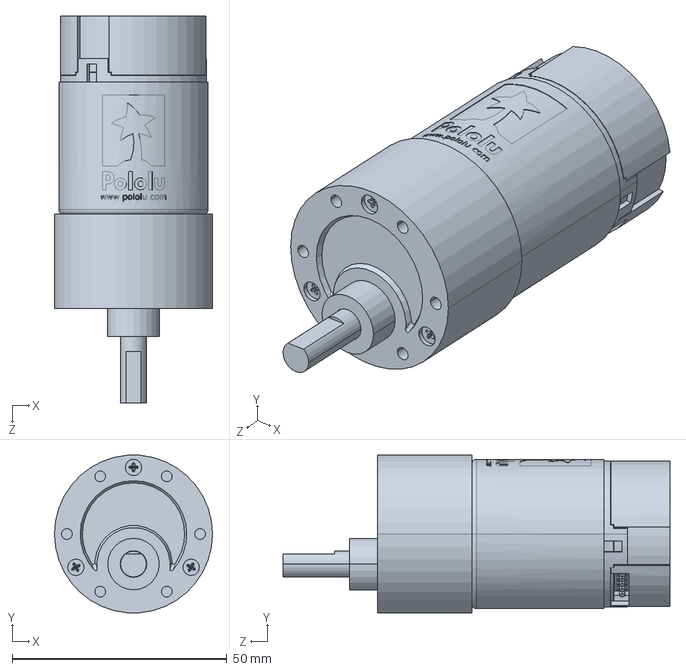
[picture p140: CAD file, 2021-05-04]
Basebot/37d-gearmotor-100-131-150-encoder.SLDPRT
36.8 x 36.7 x 90.1 mm
