mklangkamp/BeachbotsMatt/Chassis/Bucket - Bottom.SLDPRT

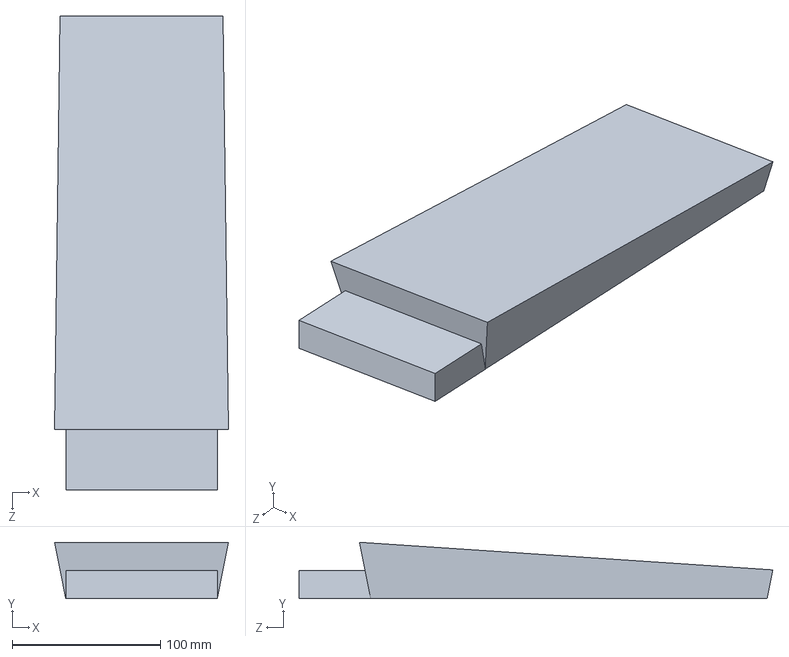
[picture p141: CAD file, 2020-11-12]
Chassis/Bucket - Bottom.SLDPRT
117.3 x 38.1 x 319.4 mm
