mklangkamp/BeachbotsMatt/Code/small_bot/Camera.py

# title           :Camera.py
# description     :Class to stream live video from the webcam
# author          :Dennis Chavez Romero
# date            :2021-03-21
# version         :0.1
# notes           :Original source: https://github.com/EdjeElectronics/TensorFlow-Lite-Object-Detection-on-Android-and-Raspberry-Pi/blob/master/TFLite_detection_webcam.py
# python_version  :3.7
# ==============================================================================

import cv2
from threading import Thread
# Define VideoStream class to handle streaming of video from webcam in separate processing thread
# Source - Adrian Rosebrock, PyImageSearch: https://www.pyimagesearch.com/2015/12/28/increasing-raspberry-pi-fps-with-python-and-opencv/
class VideoStream:
    """Camera object that controls video streaming from the Picamera"""

    def __init__(self, resolution=(640, 360), framerate=30):  # was 640,480 framerate was 30
        """
        Class constructor
        """
        # Initialize the PiCamera and the camera image stream
        self.stream = cv2.VideoCapture(0)
        ret = self.stream.set(cv2.CAP_PROP_FOURCC, cv2.VideoWriter_fourcc(*'MJPG'))
        ret = self.stream.set(3, resolution[0])
        ret = self.stream.set(4, resolution[1])

        # Read first frame from the stream
        (self.grabbed, self.frame) = self.stream.read()

        # Variable to control when the camera is
        self.stopped = False

    def start(self):
        # Start the thread that reads frames from the video stream
        Thread(target=self.update, args=()).start()
        return self

    def update(self):
        # Keep looping indefinitely until the thread is stopped
        while True:
            # If the camera is stopped, stop the thread
            if self.stopped:
                # Close camera resources
                self.stream.release()
                return

            # Otherwise, grab the next frame from the stream
            (self.grabbed, self.frame) = self.stream.read()

    def read(self):
        # Return the most recent frame
        return self.frame

    def stop(self):
        # Indicate that the camera and thread should be stopped
        self.stopped = True
